inclusionAI/Universal-Manipulation-Exoskeleton/ume/robot/ume/v6_imu/models/assets/4040_ybimu.stl

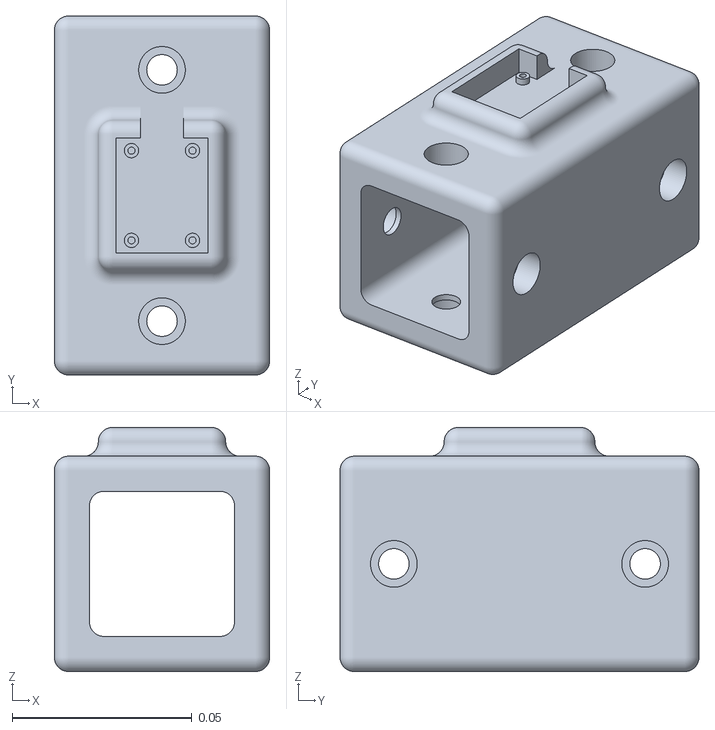
[picture p19: CAD file, 2026-07-16]
ume/robot/ume/v6_imu/models/assets/4040_ybimu.stl
0.06 x 0.1 x 0.068
