inclusionAI/Universal-Manipulation-Exoskeleton/ume/robot/openarm1/models/meshes/collision/arm/link0.stl

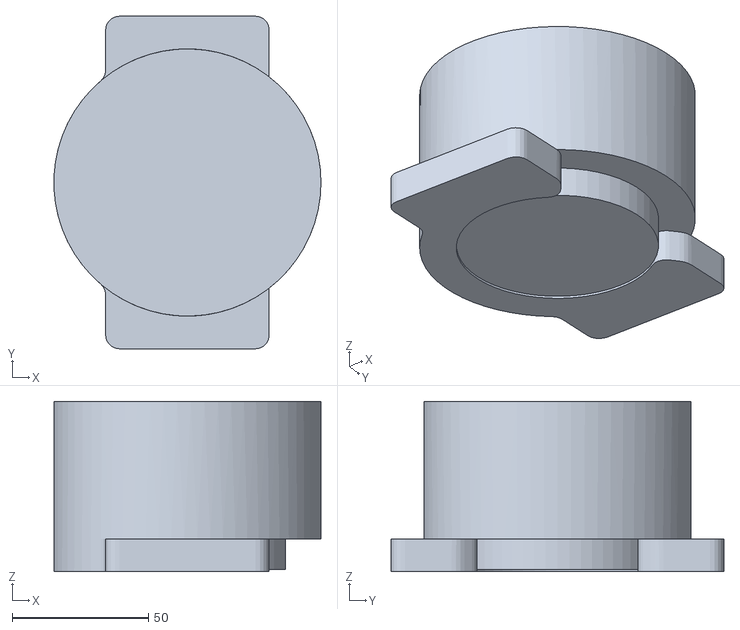
[picture p20: CAD file, 2026-07-16]
ume/robot/openarm1/models/meshes/collision/arm/link0.stl
97.9 x 122.0 x 62.5
