inclusionAI/Universal-Manipulation-Exoskeleton/ume/robot/openarm1/models/meshes/visual/arm/link5_0.obj

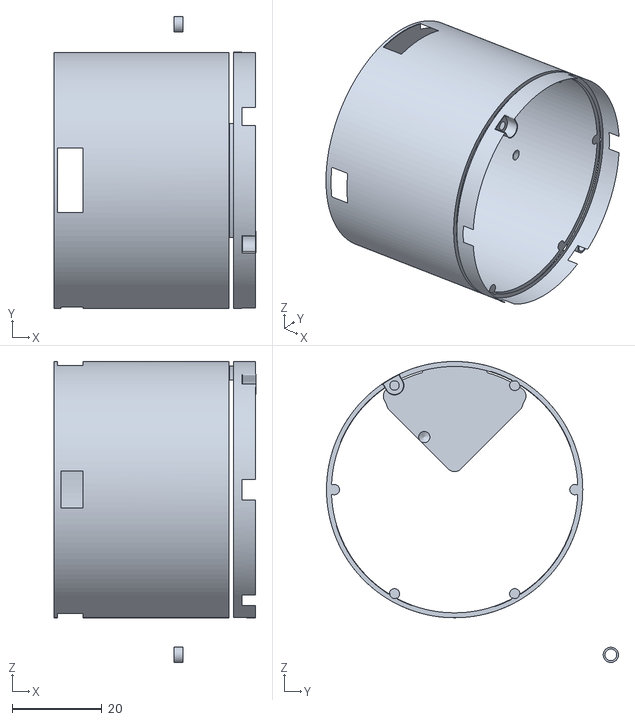
[picture p21: CAD file, 2026-07-16]
ume/robot/openarm1/models/meshes/visual/arm/link5_0.obj
44.9 x 64.9 x 66.9
