inclusionAI/Universal-Manipulation-Exoskeleton/ume/robot/openarm1/models/meshes/visual/body/body_link0_1.obj

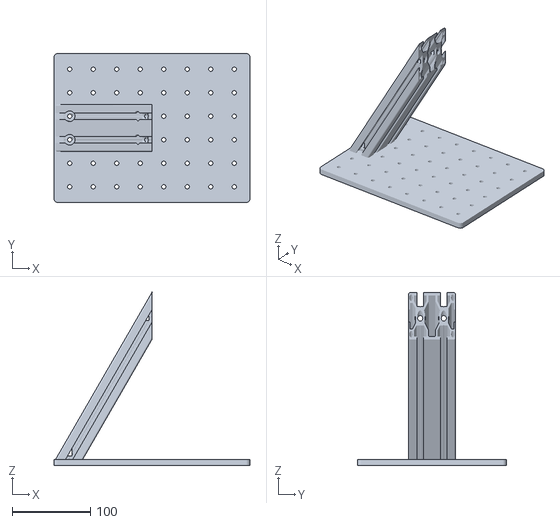
[picture p22: CAD file, 2026-07-16]
ume/robot/openarm1/models/meshes/visual/body/body_link0_1.obj
250.0 x 190.0 x 221.0
