inclusionAI/Universal-Manipulation-Exoskeleton/ume/robot/openarm1/models/meshes/visual/gripper/hand_1.obj

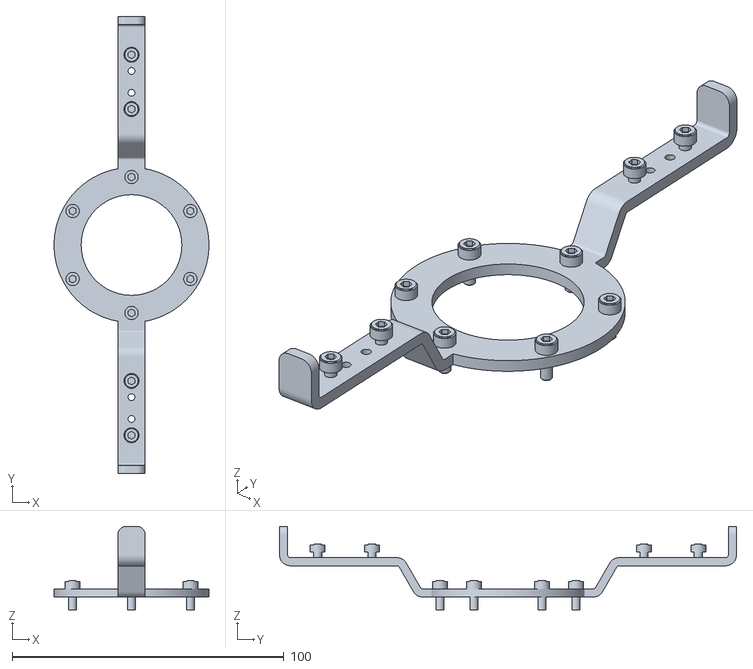
[picture p23: CAD file, 2026-07-16]
ume/robot/openarm1/models/meshes/visual/gripper/hand_1.obj
57.0 x 168.1 x 31.0
