inclusionAI/Universal-Manipulation-Exoskeleton/ume/robot/ume/v6_bimanual/models/assets/v6_xt30_2_2_50cm.stl

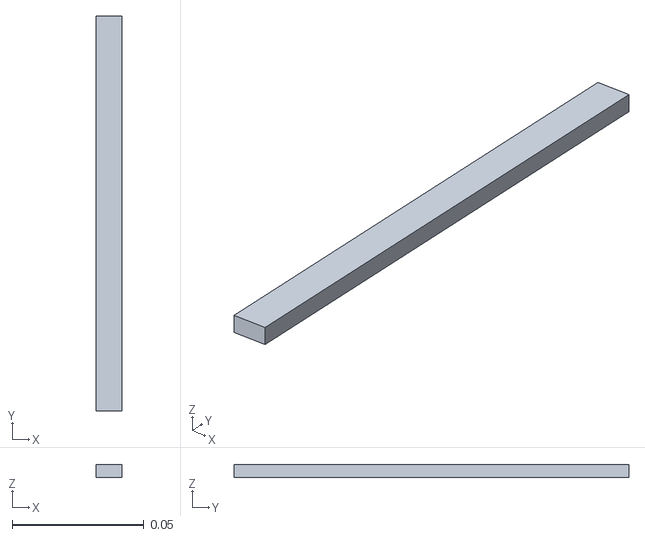
[picture p24: CAD file, 2026-07-16]
ume/robot/ume/v6_bimanual/models/assets/v6_xt30_2_2_50cm.stl
0.01 x 0.15 x 0.005
