inclusionAI/Universal-Manipulation-Exoskeleton/ume/robot/ume/v6_imu/models/assets/v6_4040_j1_loop_r.stl

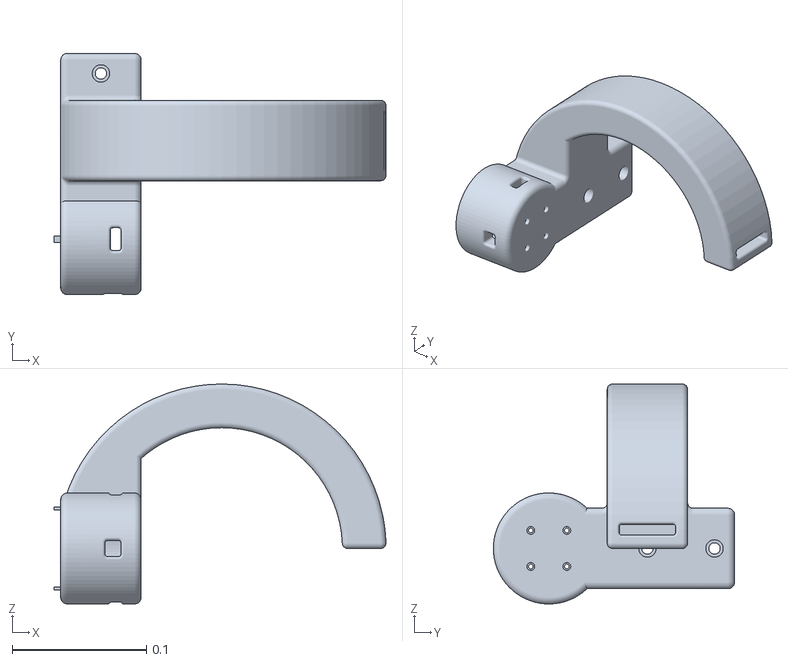
[picture p25: CAD file, 2026-07-16]
ume/robot/ume/v6_imu/models/assets/v6_4040_j1_loop_r.stl
0.248 x 0.18 x 0.164
