inclusionAI/Universal-Manipulation-Exoskeleton/ume/robot/openarm1/models/meshes/collision/arm/link1.stl

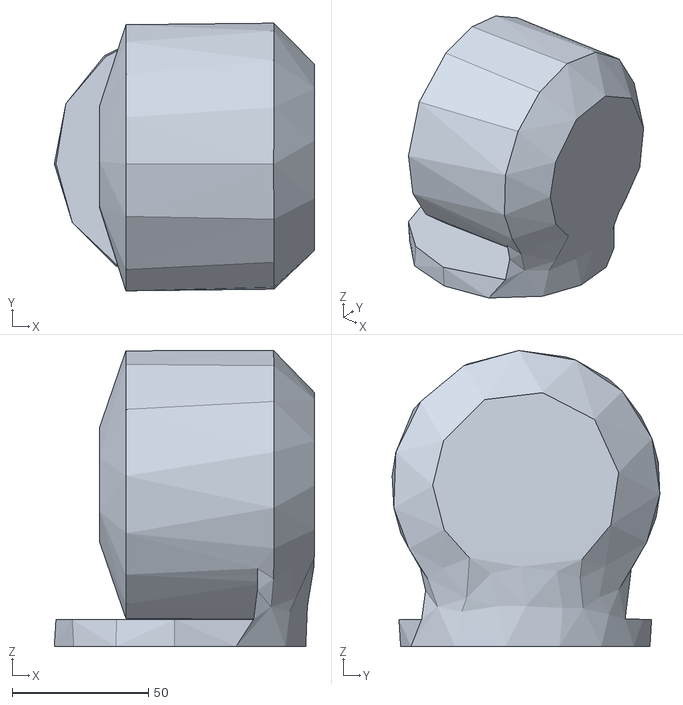
[picture p26: CAD file, 2026-07-16]
ume/robot/openarm1/models/meshes/collision/arm/link1.stl
95.7 x 98.4 x 108.8
