inclusionAI/Universal-Manipulation-Exoskeleton/ume/robot/openarm1/models/meshes/visual/arm/link2_2.obj

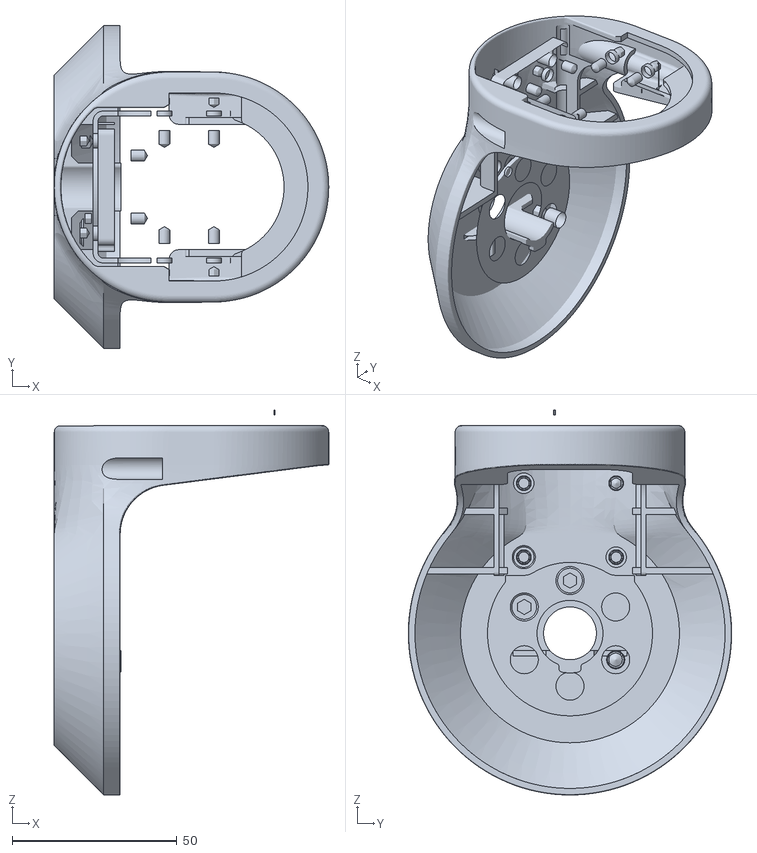
[picture p27: CAD file, 2026-07-16]
ume/robot/openarm1/models/meshes/visual/arm/link2_2.obj
83.2 x 98.0 x 116.7
