inclusionAI/Universal-Manipulation-Exoskeleton/ume/robot/openarm1/models/meshes/visual/body/body_link0_5.obj

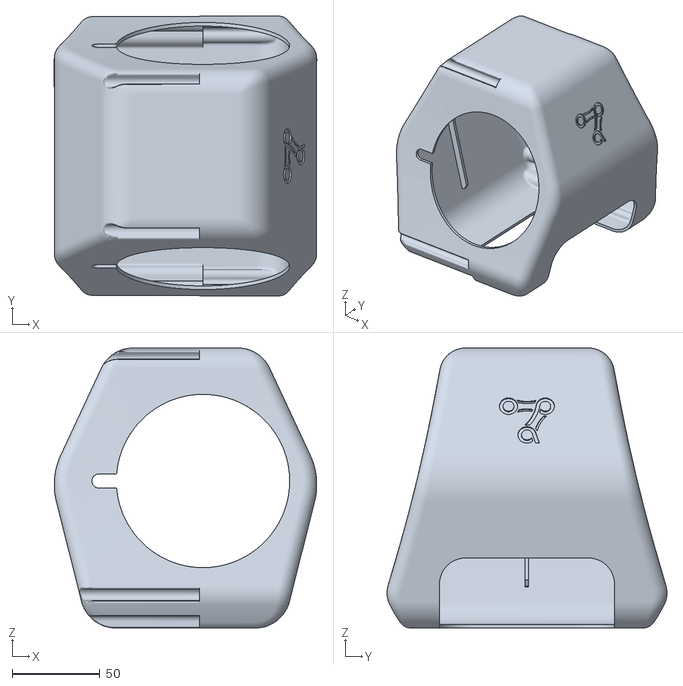
[picture p28: CAD file, 2026-07-16]
ume/robot/openarm1/models/meshes/visual/body/body_link0_5.obj
150.0 x 160.0 x 160.0
