inclusionAI/Universal-Manipulation-Exoskeleton/ume/robot/openarm1/models/meshes/visual/gripper/finger_1.obj

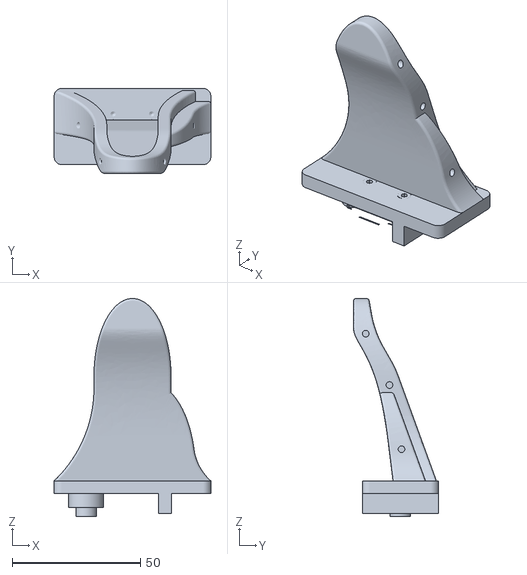
[picture p29: CAD file, 2026-07-16]
ume/robot/openarm1/models/meshes/visual/gripper/finger_1.obj
61.0 x 33.2 x 84.9
