inclusionAI/Universal-Manipulation-Exoskeleton/ume/robot/ume/ume_step/ume_v6_bimanual - v6_2020_J4_L.step

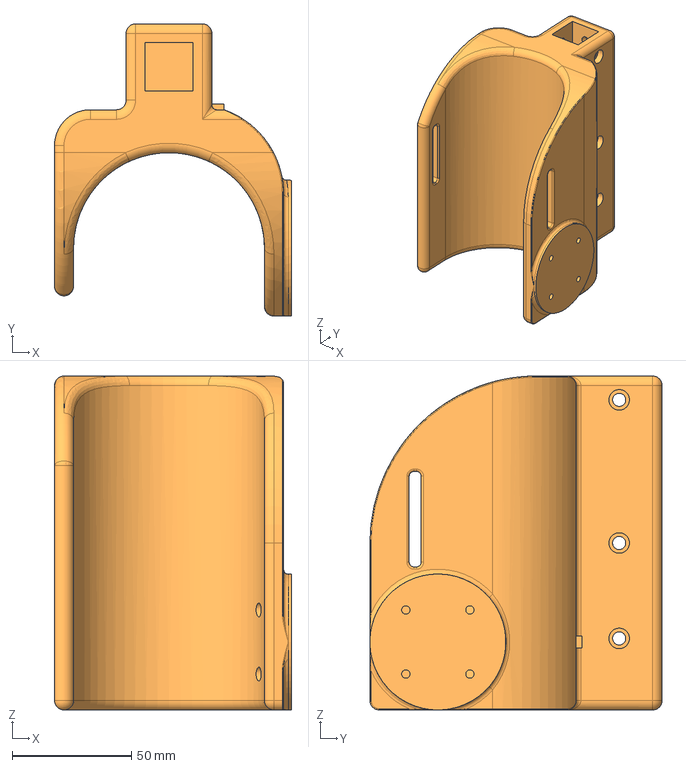
[picture p30: CAD file, 2026-07-16]
ume/robot/ume/ume_step/ume_v6_bimanual - v6_2020_J4_L.step
99.3 x 122.5 x 140.0 mm
