inclusionAI/Universal-Manipulation-Exoskeleton/ume/robot/ume/v6_bimanual/models/assets/dm_j4340_2ec.stl

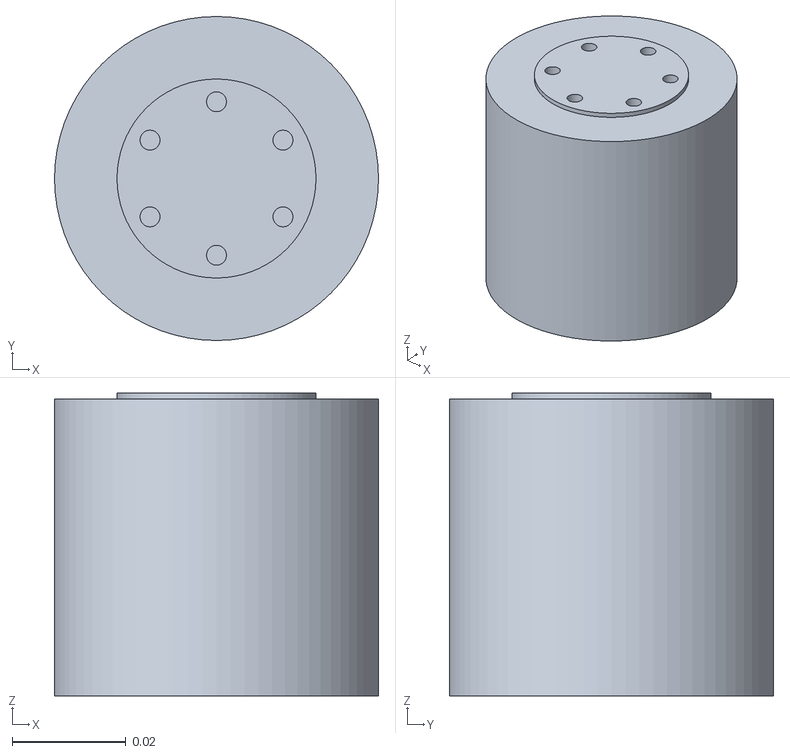
[picture p31: CAD file, 2026-07-16]
ume/robot/ume/v6_bimanual/models/assets/dm_j4340_2ec.stl
0.057 x 0.057 x 0.0533
