inclusionAI/Universal-Manipulation-Exoskeleton/ume/robot/ume/v6_imu/models/assets/v5_wrist_j6_j7.stl

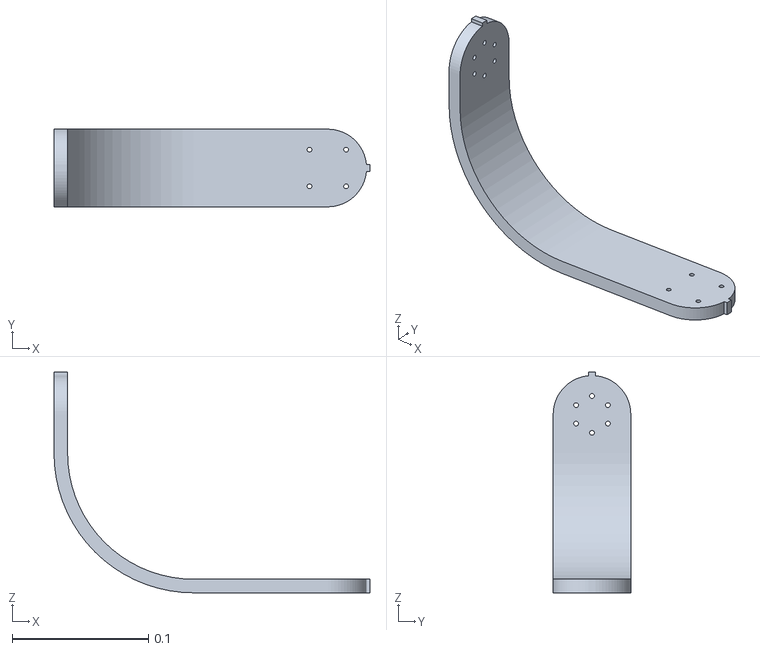
[picture p32: CAD file, 2026-07-16]
ume/robot/ume/v6_imu/models/assets/v5_wrist_j6_j7.stl
0.232 x 0.057 x 0.162
