inclusionAI/Universal-Manipulation-Exoskeleton/ume/robot/openarm1/models/meshes/collision/arm/link7.stl

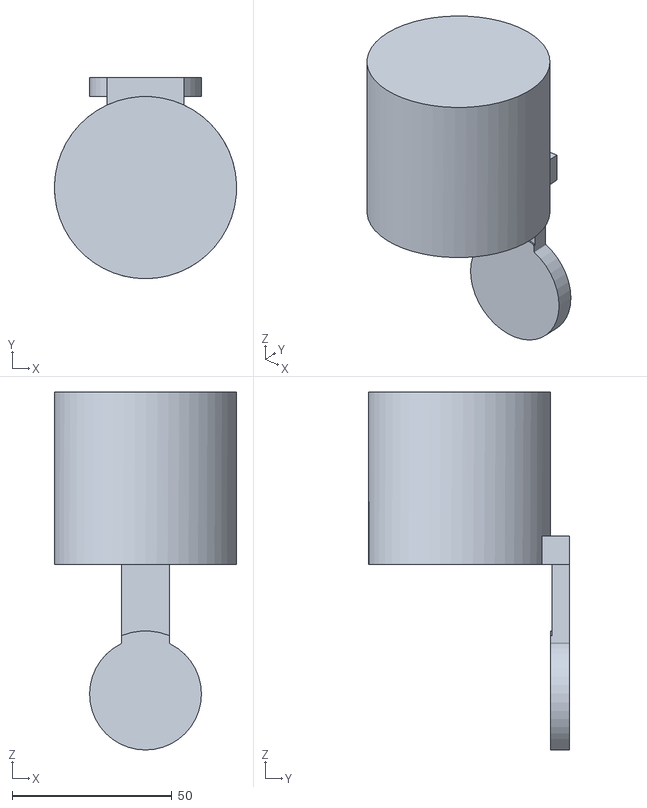
[picture p33: CAD file, 2026-07-16]
ume/robot/openarm1/models/meshes/collision/arm/link7.stl
57.0 x 63.0 x 112.0
