inclusionAI/Universal-Manipulation-Exoskeleton/ume/robot/openarm1/models/meshes/visual/arm/link7_1.obj

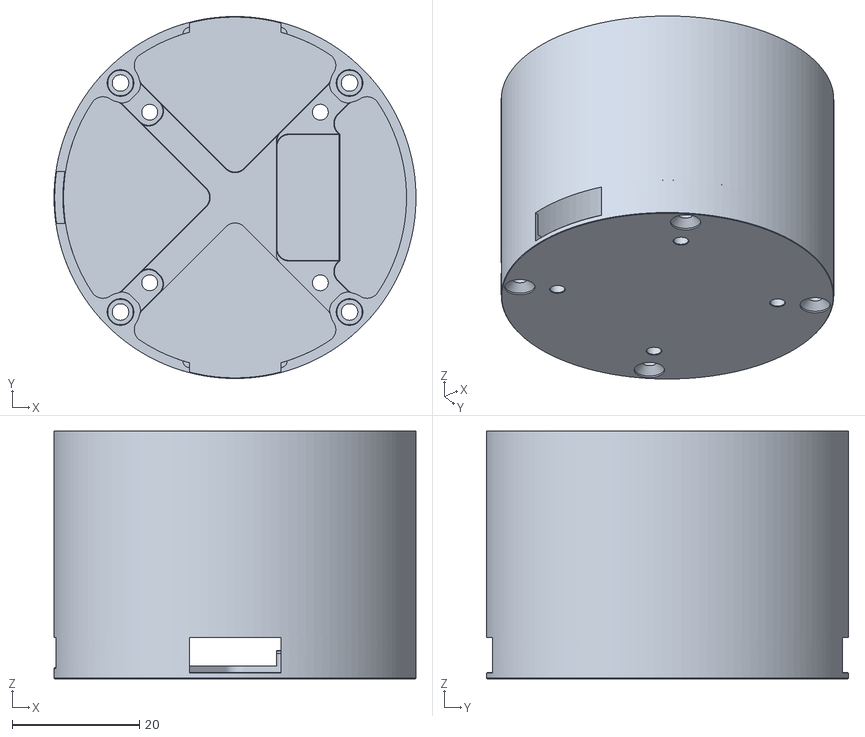
[picture p34: CAD file, 2026-07-16]
ume/robot/openarm1/models/meshes/visual/arm/link7_1.obj
57.0 x 57.0 x 39.0
