inclusionAI/Universal-Manipulation-Exoskeleton/ume/robot/openarm1/models/meshes/visual/body/body_link0_3.obj

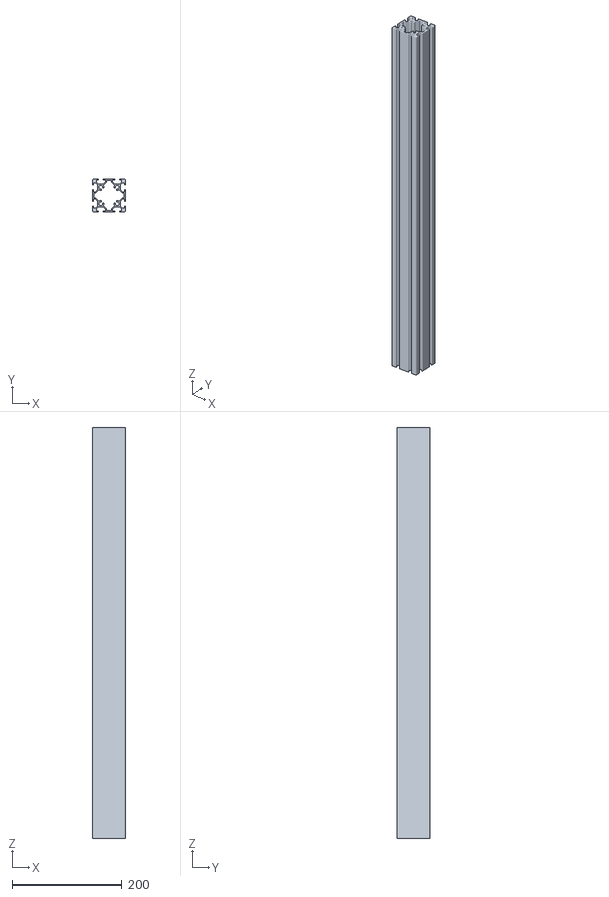
[picture p35: CAD file, 2026-07-16]
ume/robot/openarm1/models/meshes/visual/body/body_link0_3.obj
60.0 x 60.0 x 750.0
