inclusionAI/Universal-Manipulation-Exoskeleton/ume/robot/ume/v6_bimanual/models/assets/v6_wrist_j5_j6.stl

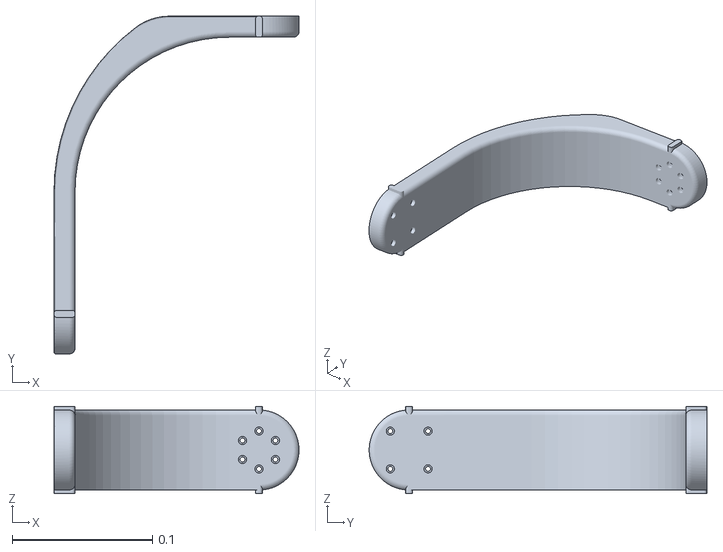
[picture p36: CAD file, 2026-07-16]
ume/robot/ume/v6_bimanual/models/assets/v6_wrist_j5_j6.stl
0.174 x 0.24 x 0.062
