inclusionAI/Universal-Manipulation-Exoskeleton/ume/robot/ume/v6_imu/models/assets/v6_20_j2.stl

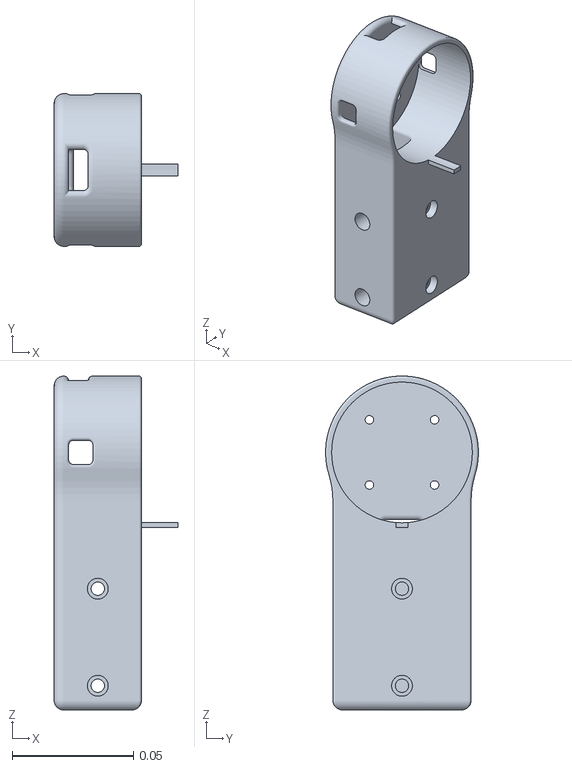
[picture p37: CAD file, 2026-07-16]
ume/robot/ume/v6_imu/models/assets/v6_20_j2.stl
0.051 x 0.063 x 0.138
