inclusionAI/Universal-Manipulation-Exoskeleton/ume/robot/openarm1/models/meshes/collision/arm/link4.stl

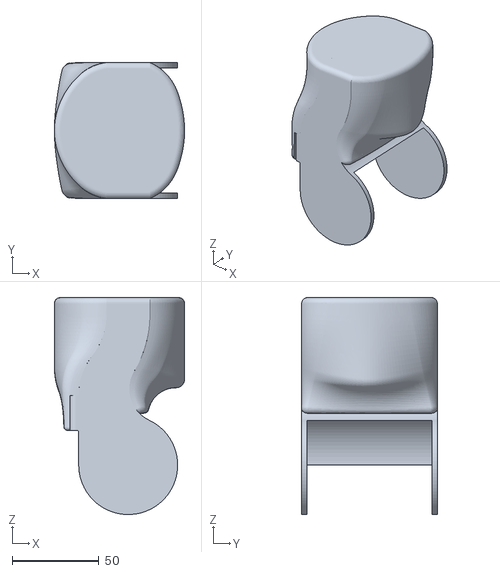
[picture p38: CAD file, 2026-07-16]
ume/robot/openarm1/models/meshes/collision/arm/link4.stl
75.0 x 78.2 x 125.0
