inclusionAI/Universal-Manipulation-Exoskeleton/ume/robot/openarm1/models/meshes/visual/arm/link4_2.obj

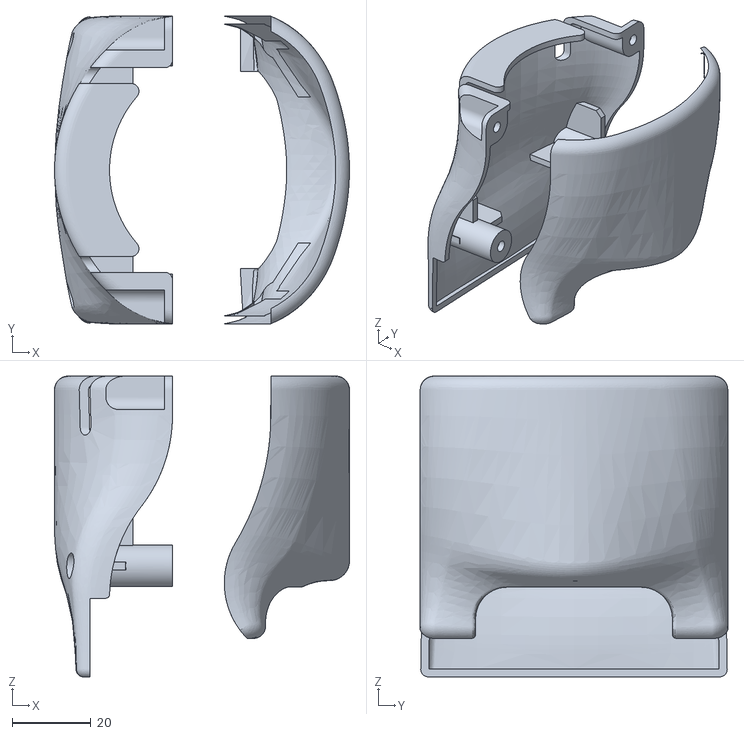
[picture p39: CAD file, 2026-07-16]
ume/robot/openarm1/models/meshes/visual/arm/link4_2.obj
75.0 x 78.2 x 76.5
