inclusionAI/Universal-Manipulation-Exoskeleton/ume/robot/openarm1/models/meshes/visual/body/body_link0_4.obj

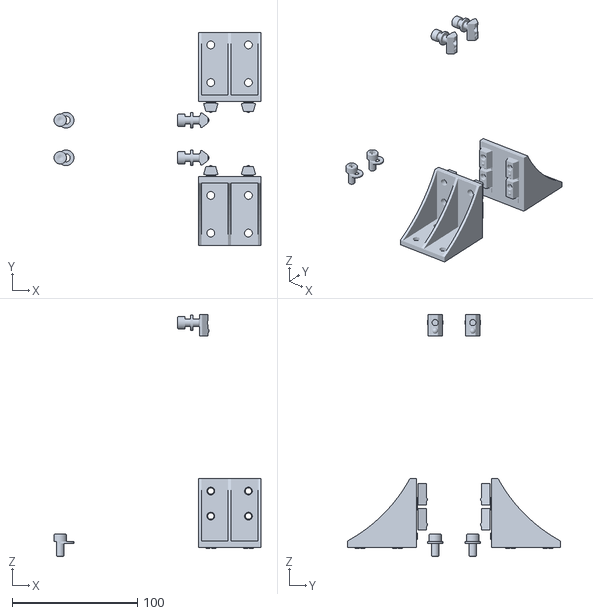
[picture p40: CAD file, 2026-07-16]
ume/robot/openarm1/models/meshes/visual/body/body_link0_4.obj
165.0 x 170.0 x 192.9
