inclusionAI/Universal-Manipulation-Exoskeleton/ume/robot/openarm1/models/meshes/collision/arm/link3.stl

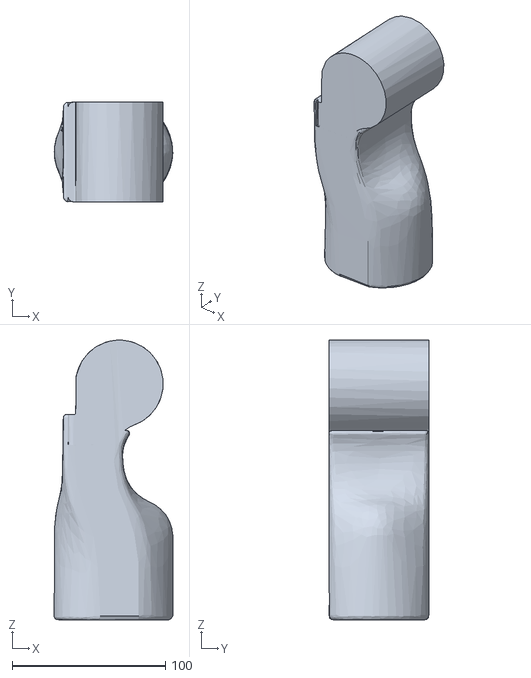
[picture p41: CAD file, 2026-07-16]
ume/robot/openarm1/models/meshes/collision/arm/link3.stl
77.3 x 65.0 x 182.6
