inclusionAI/Universal-Manipulation-Exoskeleton/ume/robot/openarm1/models/meshes/visual/arm/link1_3.obj

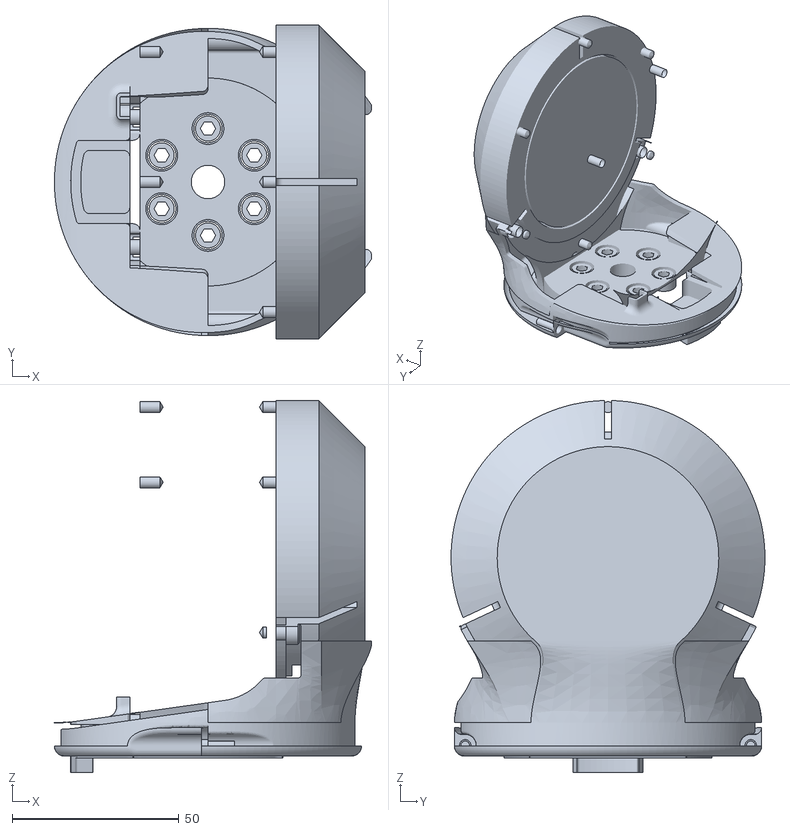
[picture p42: CAD file, 2026-07-16]
ume/robot/openarm1/models/meshes/visual/arm/link1_3.obj
95.0 x 94.0 x 111.4
