inclusionAI/Universal-Manipulation-Exoskeleton/ume/robot/ume/v6_bimanual/models/assets/v5_4040_j1.stl

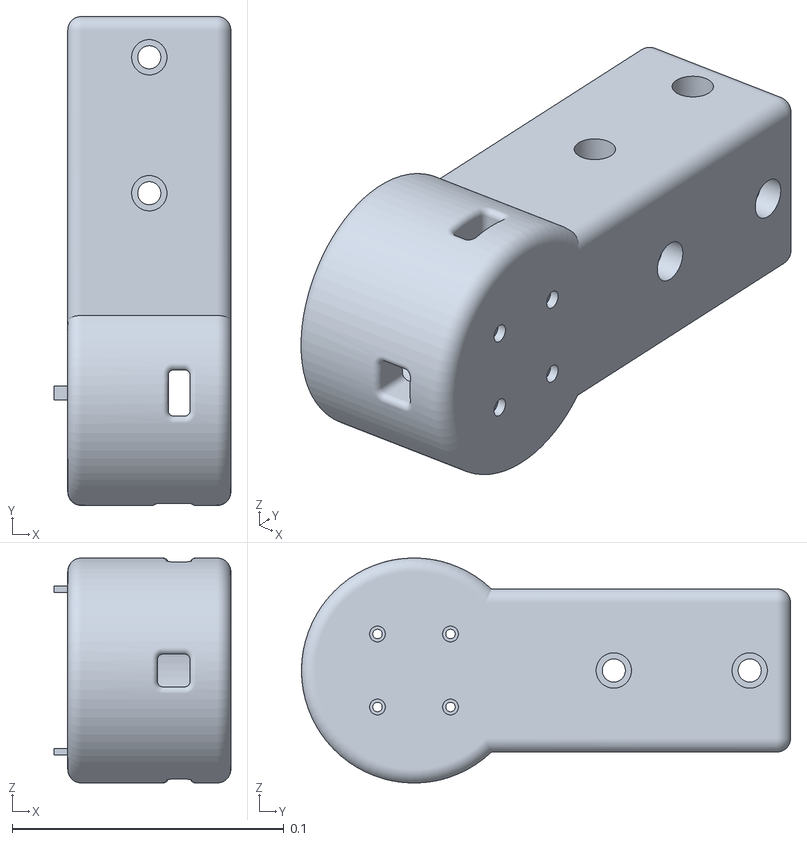
[picture p43: CAD file, 2026-07-16]
ume/robot/ume/v6_bimanual/models/assets/v5_4040_j1.stl
0.065 x 0.18 x 0.0828
