inclusionAI/Universal-Manipulation-Exoskeleton/ume/robot/openarm1/models/meshes/collision/arm/link5.stl

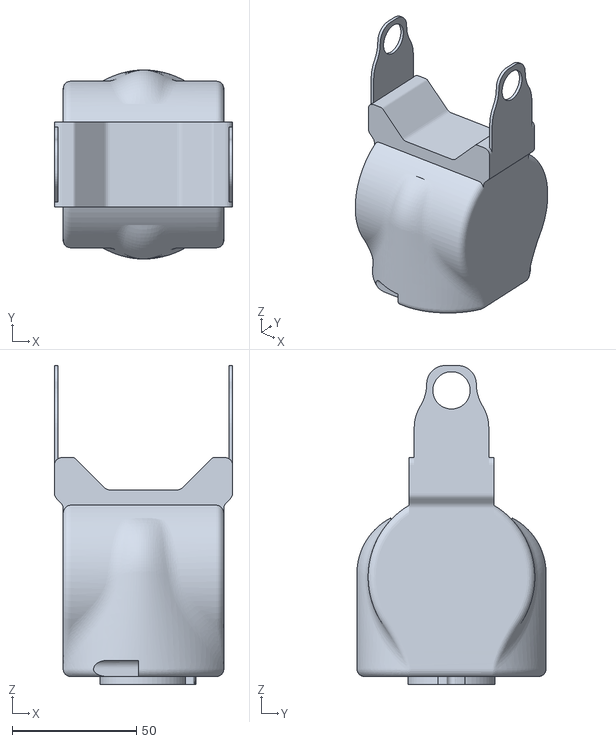
[picture p44: CAD file, 2026-07-16]
ume/robot/openarm1/models/meshes/collision/arm/link5.stl
71.6 x 76.0 x 128.2
