inclusionAI/Universal-Manipulation-Exoskeleton/ume/robot/openarm1/models/meshes/visual/arm/link1_1.obj

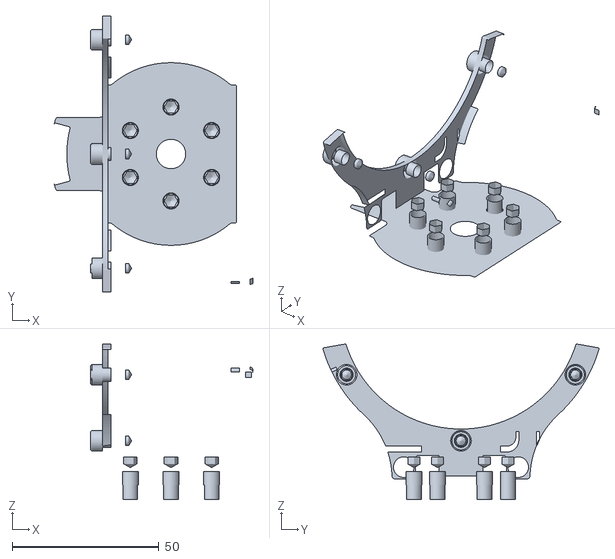
[picture p45: CAD file, 2026-07-16]
ume/robot/openarm1/models/meshes/visual/arm/link1_1.obj
67.7 x 94.0 x 53.4
