inclusionAI/Universal-Manipulation-Exoskeleton/ume/robot/openarm1/models/meshes/visual/arm/link3_2.obj

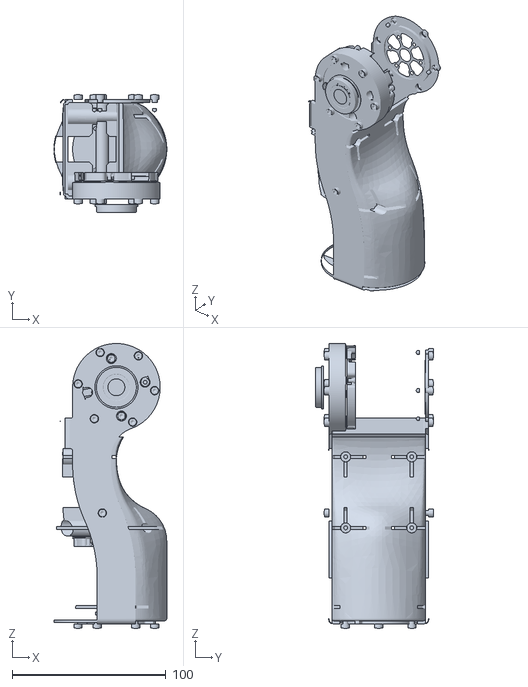
[picture p46: CAD file, 2026-07-16]
ume/robot/openarm1/models/meshes/visual/arm/link3_2.obj
73.3 x 76.5 x 185.5
