inclusionAI/Universal-Manipulation-Exoskeleton/ume/robot/ume/v6_bimanual/models/assets/v6_2020_j4_r.stl

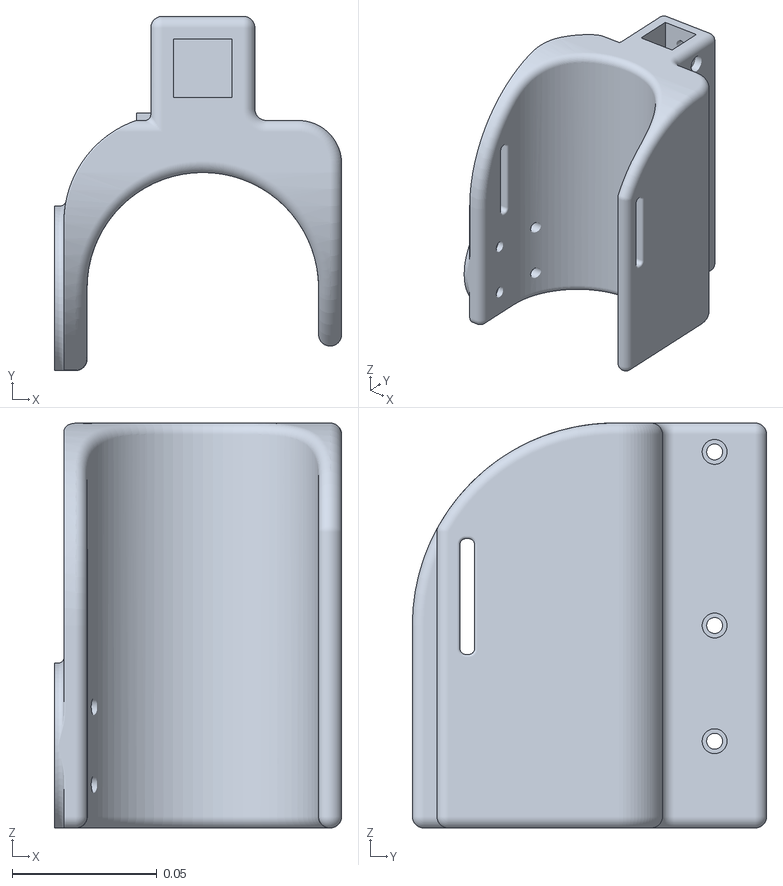
[picture p47: CAD file, 2026-07-16]
ume/robot/ume/v6_bimanual/models/assets/v6_2020_j4_r.stl
0.0994 x 0.123 x 0.14
