inclusionAI/Universal-Manipulation-Exoskeleton/ume/robot/ume/v6_imu/models/assets/4040_t_bracket.stl

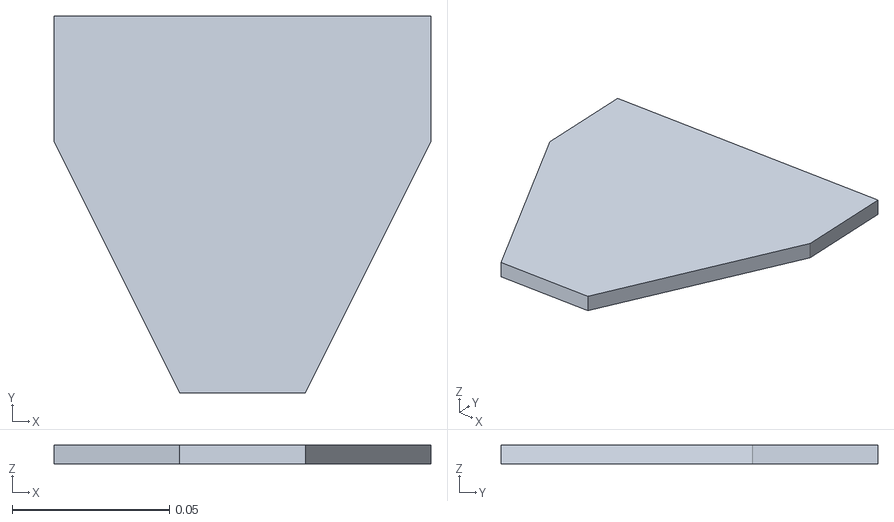
[picture p48: CAD file, 2026-07-16]
ume/robot/ume/v6_imu/models/assets/4040_t_bracket.stl
0.12 x 0.12 x 0.006
