inclusionAI/Universal-Manipulation-Exoskeleton/ume/robot/openarm1/models/meshes/visual/arm/link1_0.obj

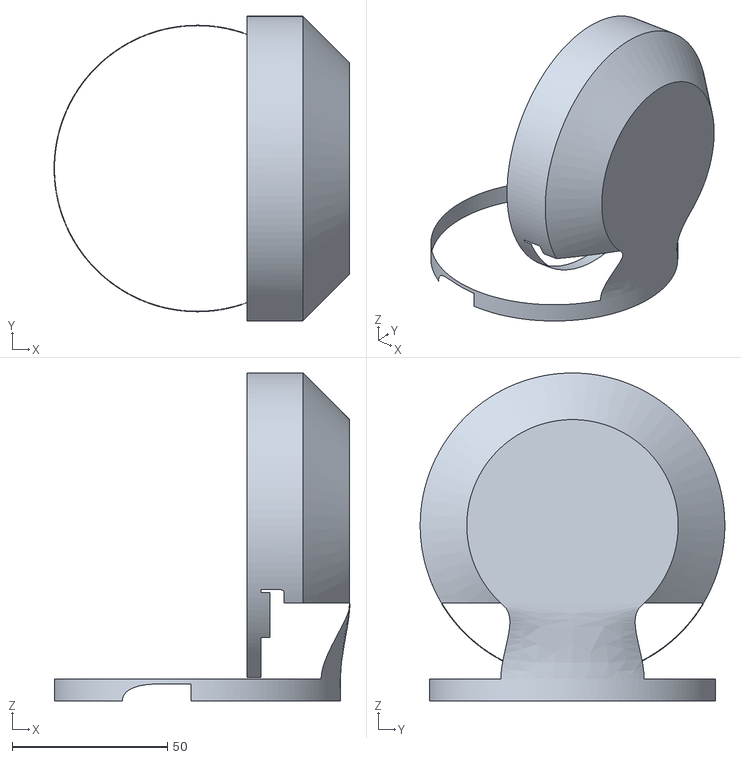
[picture p49: CAD file, 2026-07-16]
ume/robot/openarm1/models/meshes/visual/arm/link1_0.obj
95.0 x 98.0 x 105.5
