inclusionAI/Universal-Manipulation-Exoskeleton/ume/robot/ume/v6_bimanual/models/assets/v6_20_j3.stl

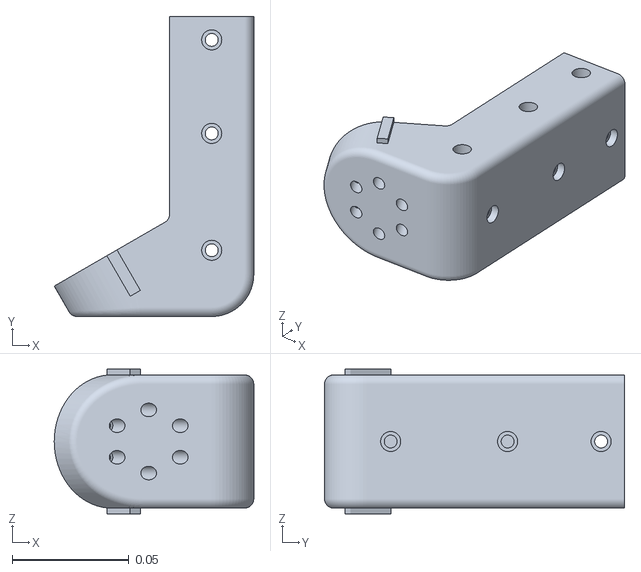
[picture p50: CAD file, 2026-07-16]
ume/robot/ume/v6_bimanual/models/assets/v6_20_j3.stl
0.0854 x 0.128 x 0.062
