inclusionAI/Universal-Manipulation-Exoskeleton/ume/robot/ume/v6_imu/models/assets/dm_j4310_2ec.stl

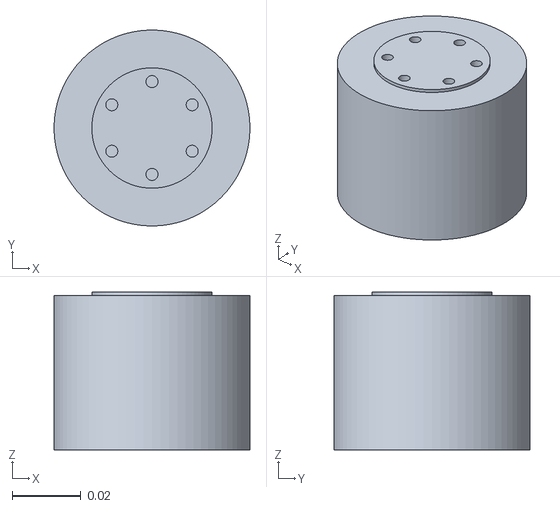
[picture p51: CAD file, 2026-07-16]
ume/robot/ume/v6_imu/models/assets/dm_j4310_2ec.stl
0.057 x 0.057 x 0.0459
