inclusionAI/Universal-Manipulation-Exoskeleton/ume/robot/openarm1/models/meshes/visual/arm/link5_2.obj

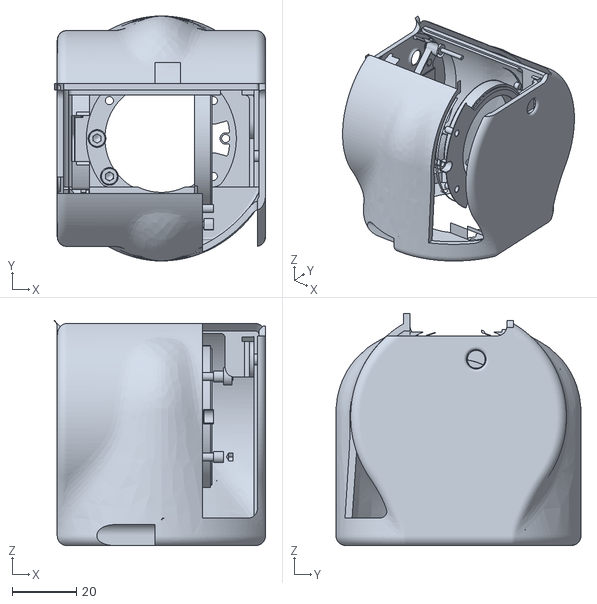
[picture p52: CAD file, 2026-07-16]
ume/robot/openarm1/models/meshes/visual/arm/link5_2.obj
65.5 x 76.0 x 72.0
