inclusionAI/Universal-Manipulation-Exoskeleton/ume/robot/openarm1/models/meshes/visual/arm/link3_0.obj

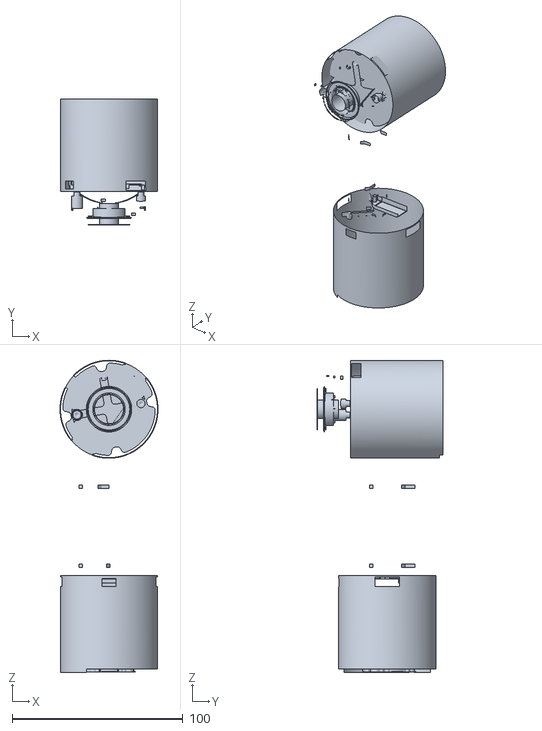
[picture p53: CAD file, 2026-07-16]
ume/robot/openarm1/models/meshes/visual/arm/link3_0.obj
57.0 x 73.5 x 182.5
