inclusionAI/Universal-Manipulation-Exoskeleton/ume/robot/ume/v6_bimanual/models/assets/v6_j1_20.stl

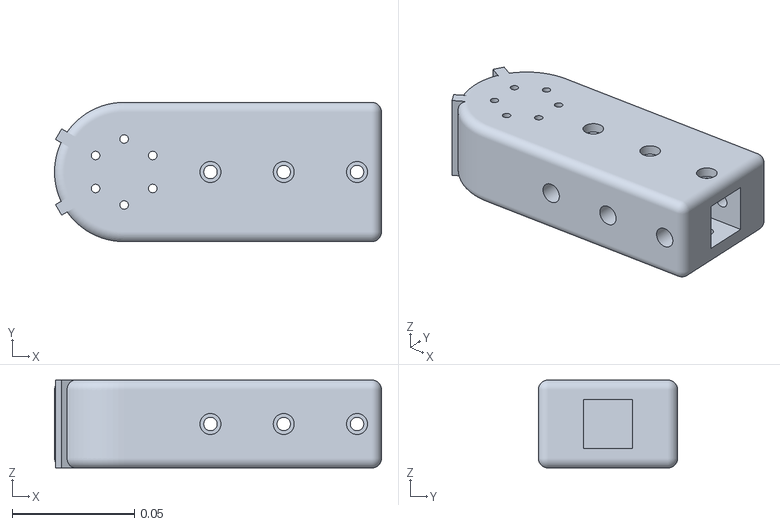
[picture p54: CAD file, 2026-07-16]
ume/robot/ume/v6_bimanual/models/assets/v6_j1_20.stl
0.134 x 0.057 x 0.036
