inclusionAI/Universal-Manipulation-Exoskeleton/ume/robot/openarm1/models/meshes/visual/arm/link2_0.obj

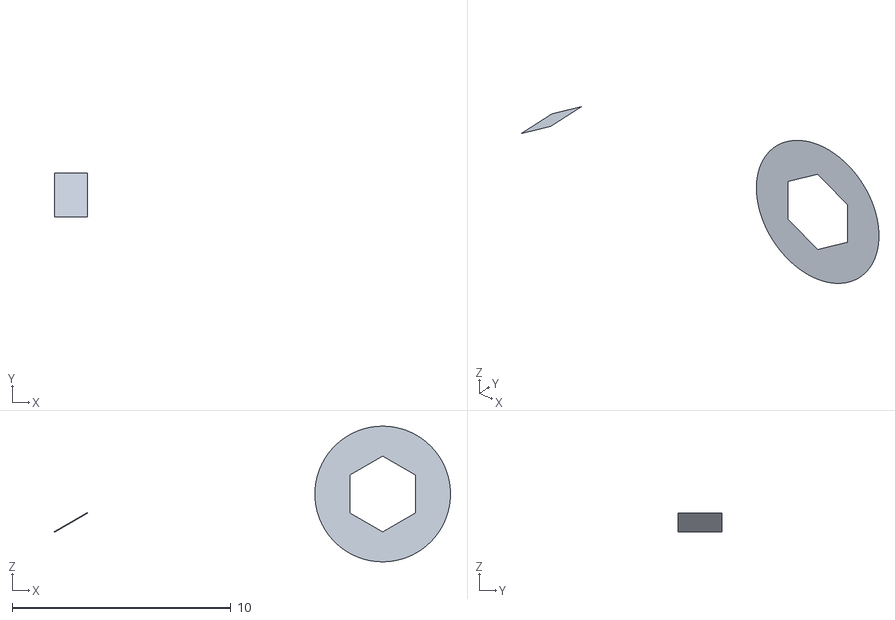
[picture p55: CAD file, 2026-07-16]
ume/robot/openarm1/models/meshes/visual/arm/link2_0.obj
18.1 x 2.00 x 6.20
