inclusionAI/Universal-Manipulation-Exoskeleton/ume/robot/ume/ume_step/ume_v6_bimanual - 2020x10cm.step

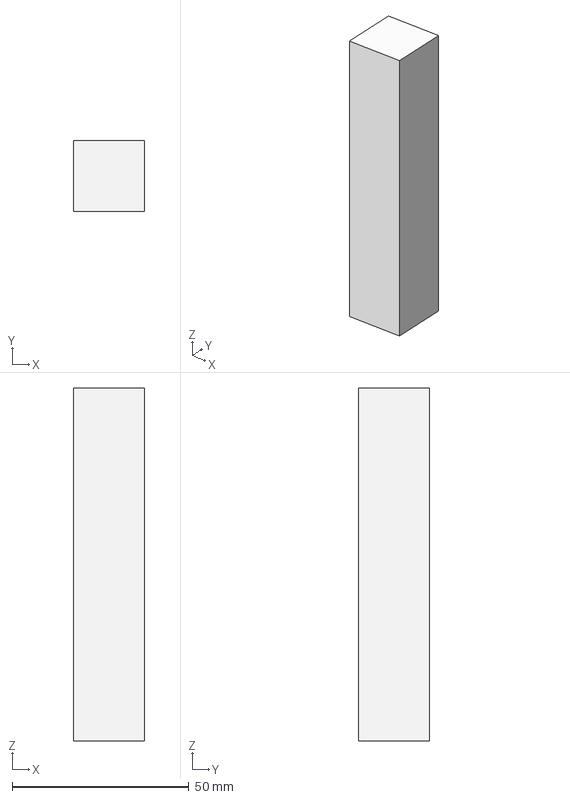
[picture p56: CAD file, 2026-07-16]
ume/robot/ume/ume_step/ume_v6_bimanual - 2020x10cm.step
20.0 x 20.0 x 100.0 mm
