inclusionAI/Universal-Manipulation-Exoskeleton/ume/robot/ume/v6_bimanual/models/assets/v6_j3_2020_l.stl

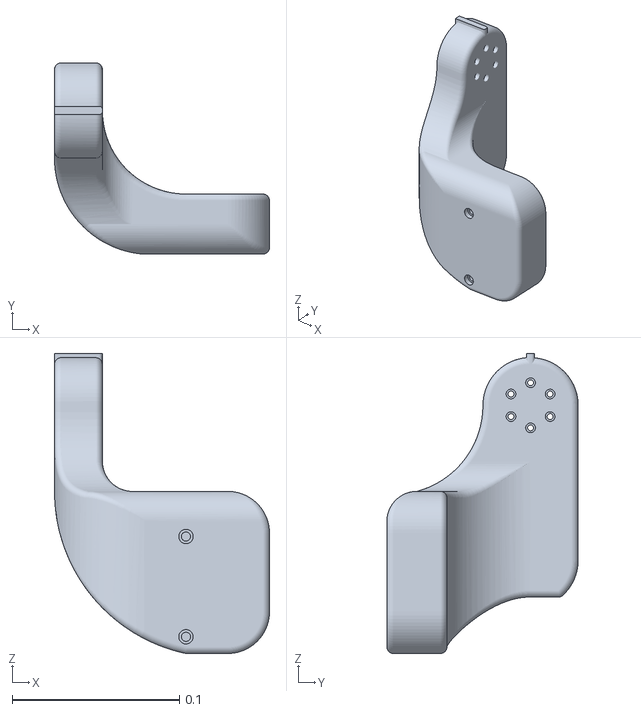
[picture p57: CAD file, 2026-07-16]
ume/robot/ume/v6_bimanual/models/assets/v6_j3_2020_l.stl
0.129 x 0.115 x 0.179
