inclusionAI/Universal-Manipulation-Exoskeleton/ume/robot/openarm1/models/meshes/visual/arm/link7_0.obj

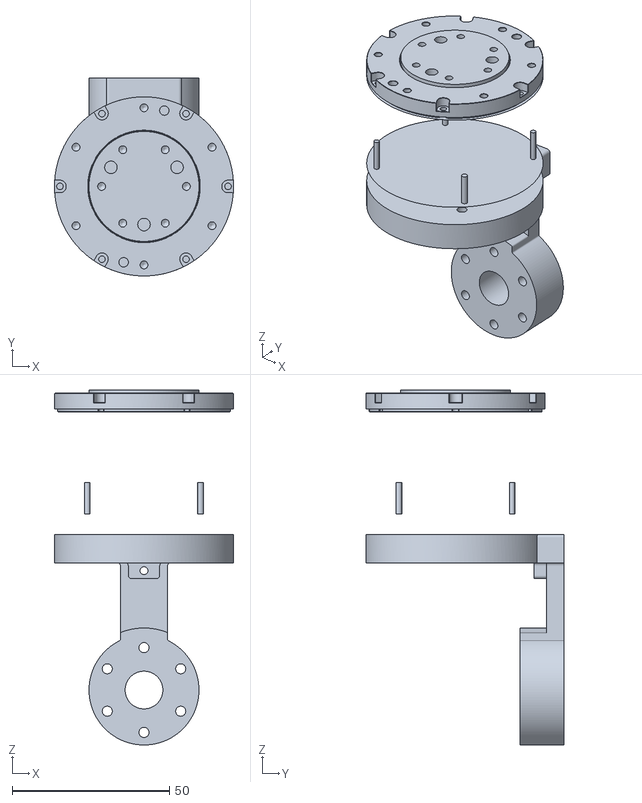
[picture p58: CAD file, 2026-07-16]
ume/robot/openarm1/models/meshes/visual/arm/link7_0.obj
57.0 x 63.0 x 113.0
