inclusionAI/Universal-Manipulation-Exoskeleton/ume/robot/openarm1/models/meshes/visual/arm/link4_0.obj

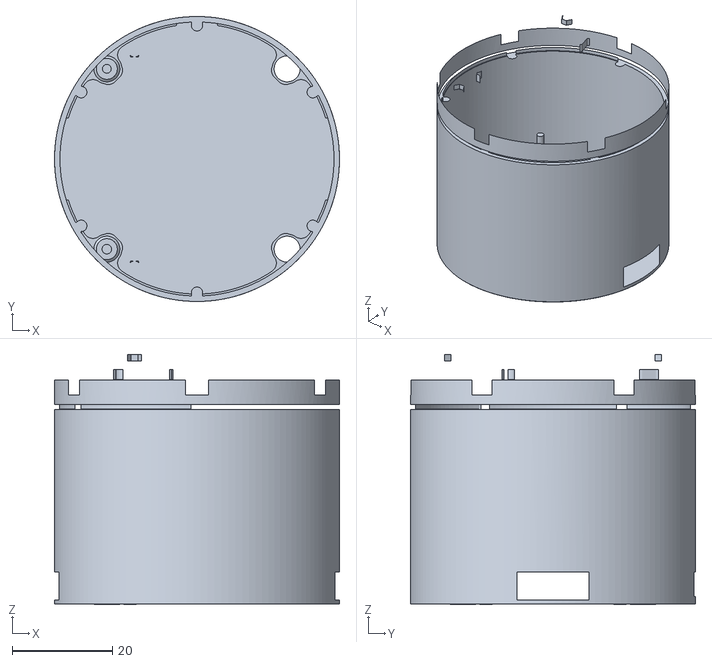
[picture p59: CAD file, 2026-07-16]
ume/robot/openarm1/models/meshes/visual/arm/link4_0.obj
57.0 x 57.0 x 50.0
