inclusionAI/Universal-Manipulation-Exoskeleton/ume/robot/openarm1/models/meshes/visual/arm/link5_1.obj

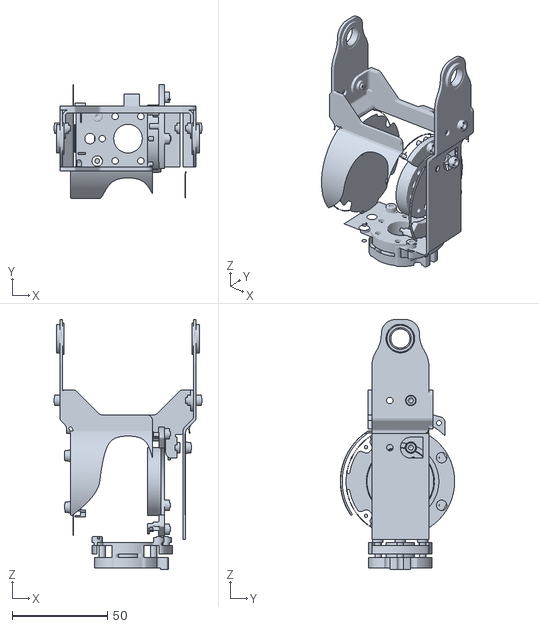
[picture p60: CAD file, 2026-07-16]
ume/robot/openarm1/models/meshes/visual/arm/link5_1.obj
77.6 x 60.0 x 131.2
