inclusionAI/Universal-Manipulation-Exoskeleton/ume/robot/ume/ume_step/ume_v6_bimanual - v5_J8_4finger.step

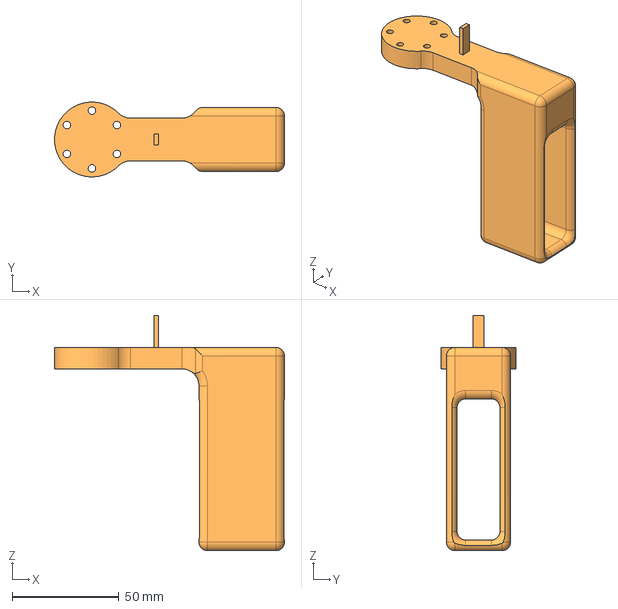
[picture p61: CAD file, 2026-07-16]
ume/robot/ume/ume_step/ume_v6_bimanual - v5_J8_4finger.step
107.5 x 35.0 x 110.0 mm
