inclusionAI/Universal-Manipulation-Exoskeleton/ume/robot/openarm1/models/meshes/visual/arm/link4_1.obj

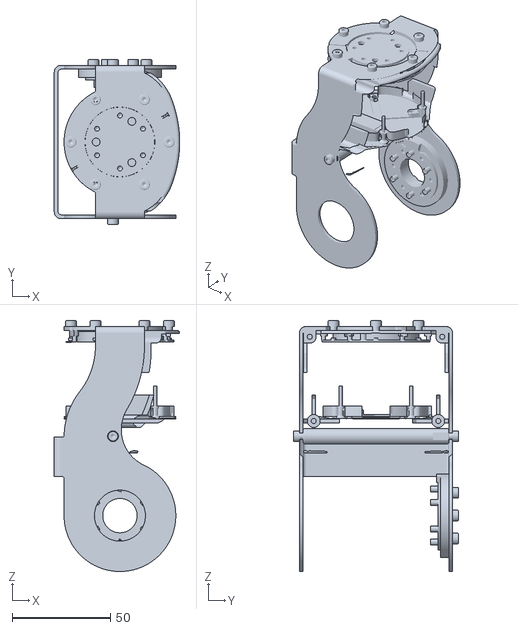
[picture p62: CAD file, 2026-07-16]
ume/robot/openarm1/models/meshes/visual/arm/link4_1.obj
64.0 x 84.2 x 128.0
