inclusionAI/Universal-Manipulation-Exoskeleton/ume/robot/ume/v6_bimanual/models/assets/v5_wrist_j7_leader_gripper_r.stl

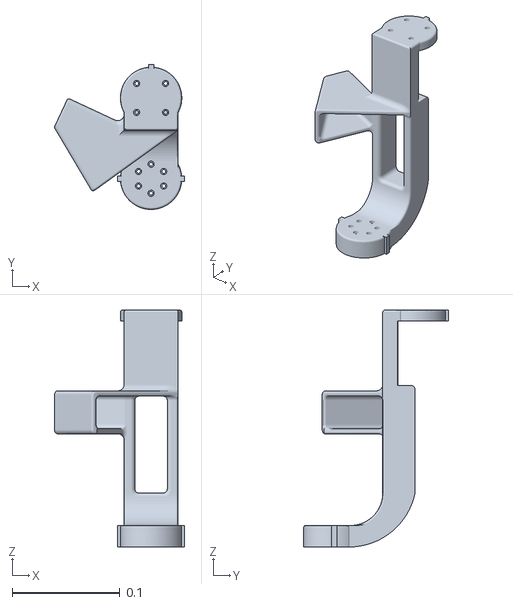
[picture p63: CAD file, 2026-07-16]
ume/robot/ume/v6_bimanual/models/assets/v5_wrist_j7_leader_gripper_r.stl
0.121 x 0.134 x 0.22
