inclusionAI/Universal-Manipulation-Exoskeleton/ume/robot/openarm1/models/meshes/visual/arm/link0_1.obj

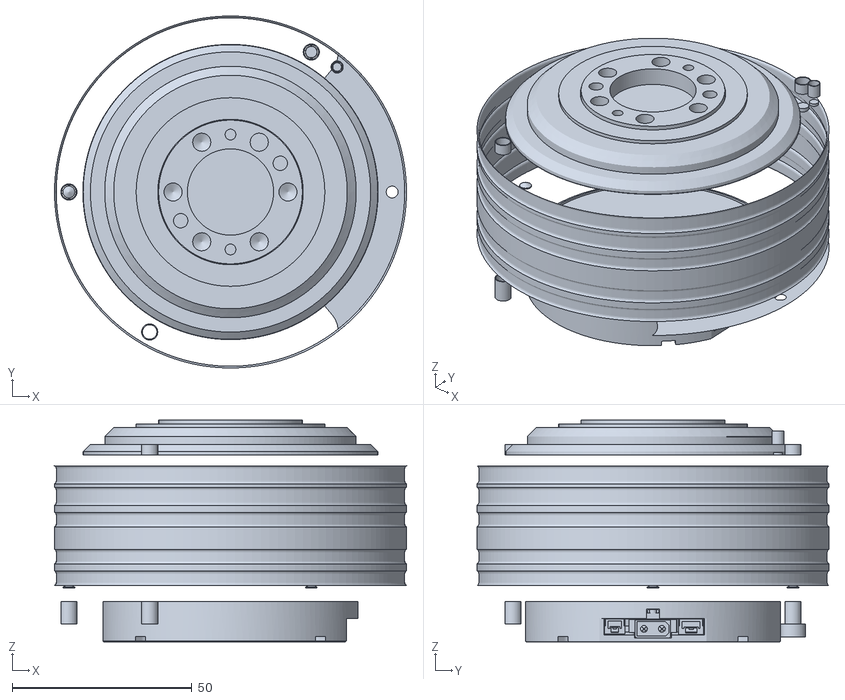
[picture p64: CAD file, 2026-07-16]
ume/robot/openarm1/models/meshes/visual/arm/link0_1.obj
98.0 x 98.0 x 61.7
