inclusionAI/Universal-Manipulation-Exoskeleton/ume/robot/ume/v6_bimanual/models/assets/v5_j8_4finger.stl

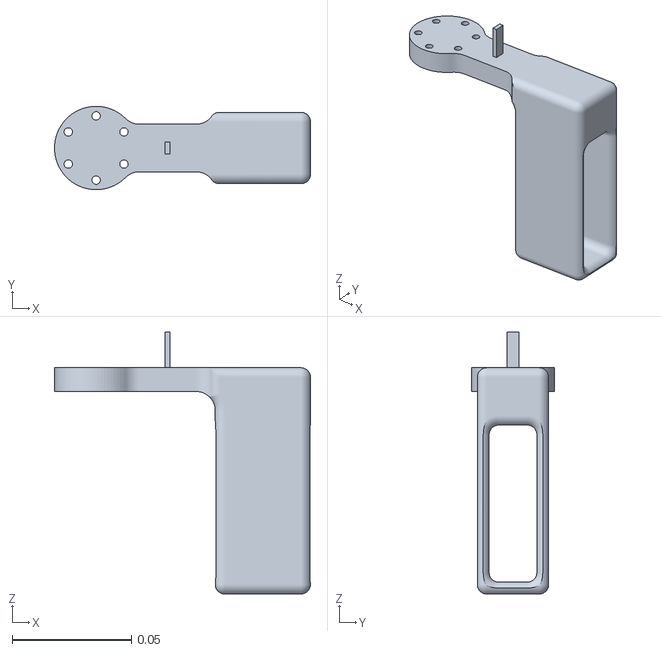
[picture p65: CAD file, 2026-07-16]
ume/robot/ume/v6_bimanual/models/assets/v5_j8_4finger.stl
0.107 x 0.035 x 0.11
