inclusionAI/Universal-Manipulation-Exoskeleton/ume/robot/openarm1/models/meshes/visual/arm/link6_0.obj

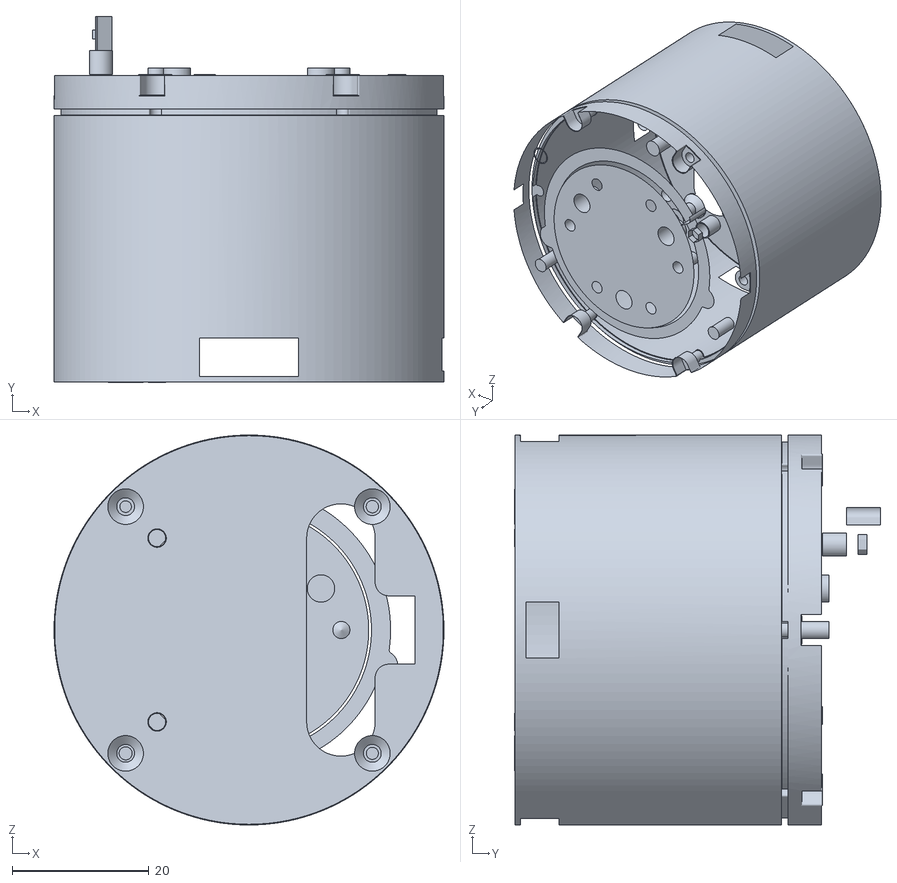
[picture p66: CAD file, 2026-07-16]
ume/robot/openarm1/models/meshes/visual/arm/link6_0.obj
57.0 x 53.5 x 57.0
