inclusionAI/Universal-Manipulation-Exoskeleton/ume/robot/openarm1/models/meshes/visual/arm/link1_2.obj

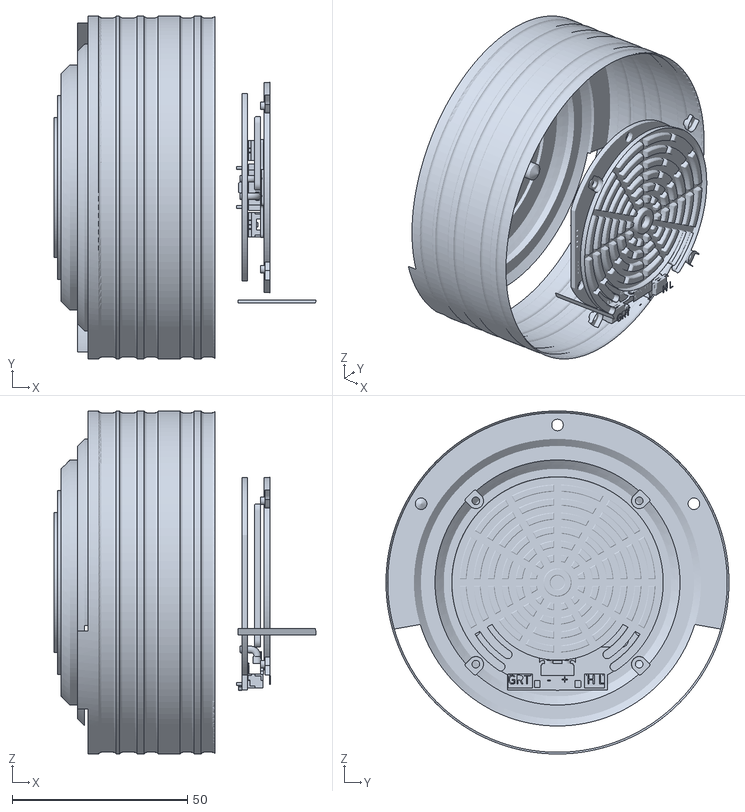
[picture p67: CAD file, 2026-07-16]
ume/robot/openarm1/models/meshes/visual/arm/link1_2.obj
74.8 x 98.0 x 98.0
