inclusionAI/Universal-Manipulation-Exoskeleton/ume/robot/ume/ume_step/ume_v6_bimanual - v6_J1_20.step

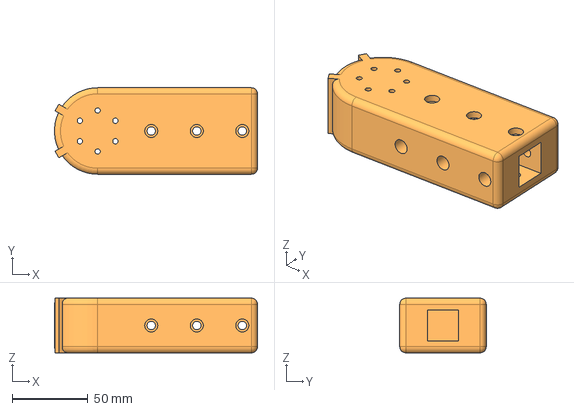
[picture p68: CAD file, 2026-07-16]
ume/robot/ume/ume_step/ume_v6_bimanual - v6_J1_20.step
133.7 x 57.0 x 36.0 mm
