inclusionAI/Universal-Manipulation-Exoskeleton/ume/robot/ume/ume_step/ume_v6_bimanual - v6_20_J2.step

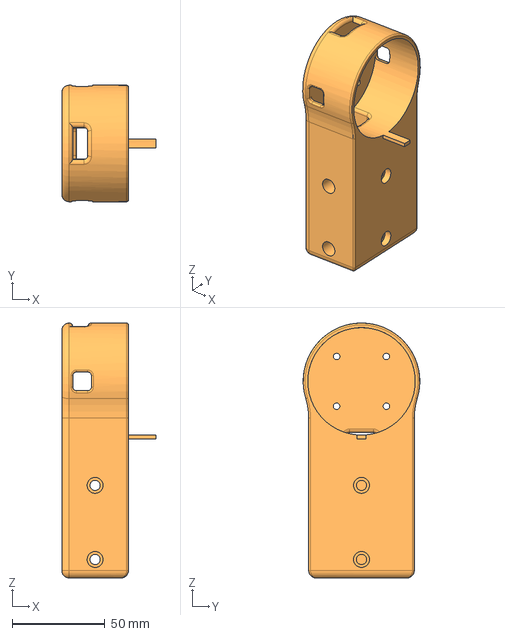
[picture p69: CAD file, 2026-07-16]
ume/robot/ume/ume_step/ume_v6_bimanual - v6_20_J2.step
51.0 x 63.0 x 137.7 mm
