inclusionAI/Universal-Manipulation-Exoskeleton/ume/robot/openarm1/models/meshes/visual/arm/link0_0.obj

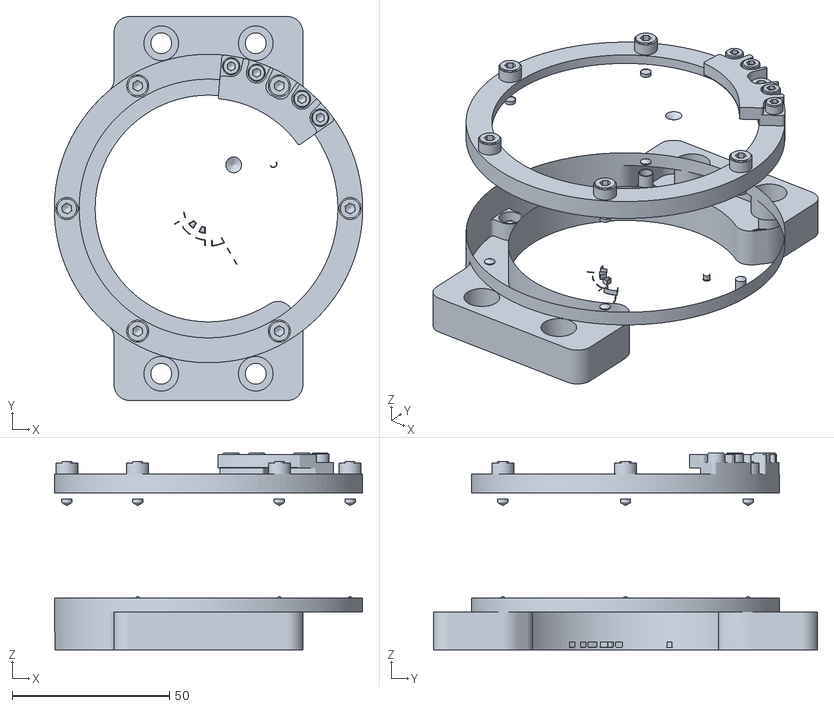
[picture p70: CAD file, 2026-07-16]
ume/robot/openarm1/models/meshes/visual/arm/link0_0.obj
98.0 x 122.0 x 62.5
