inclusionAI/Universal-Manipulation-Exoskeleton/ume/robot/ume/ume_step/ume_v6_bimanual - v6_J2_20.step

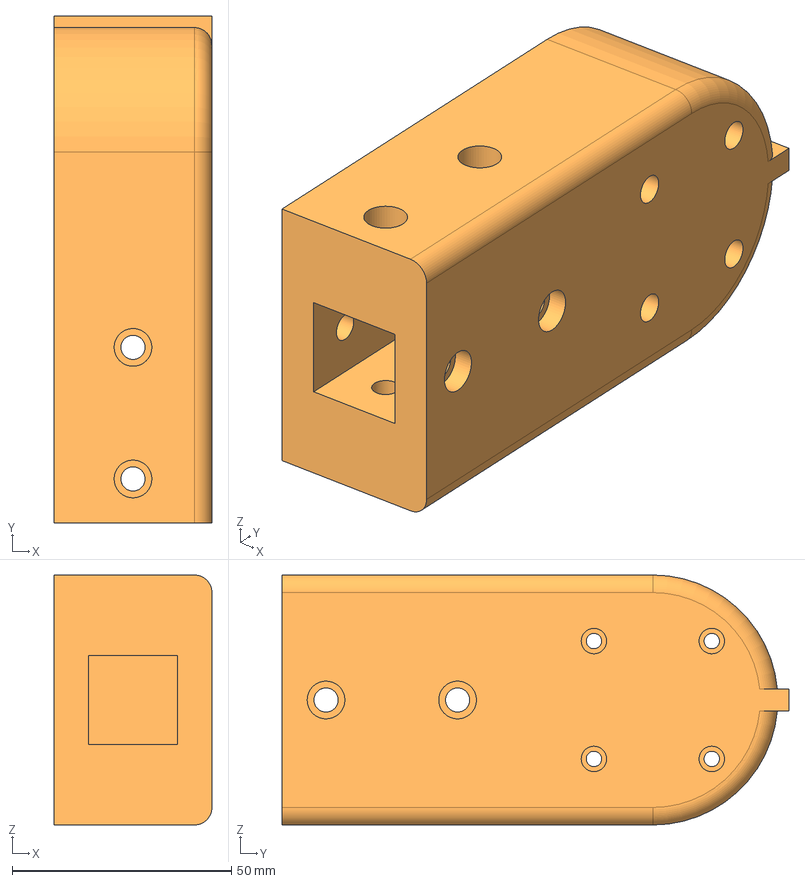
[picture p71: CAD file, 2026-07-16]
ume/robot/ume/ume_step/ume_v6_bimanual - v6_J2_20.step
36.0 x 115.5 x 57.0 mm
