inclusionAI/Universal-Manipulation-Exoskeleton/ume/robot/ume/ume_step/ume_v6_bimanual - v6_wrist_J5_J6.step

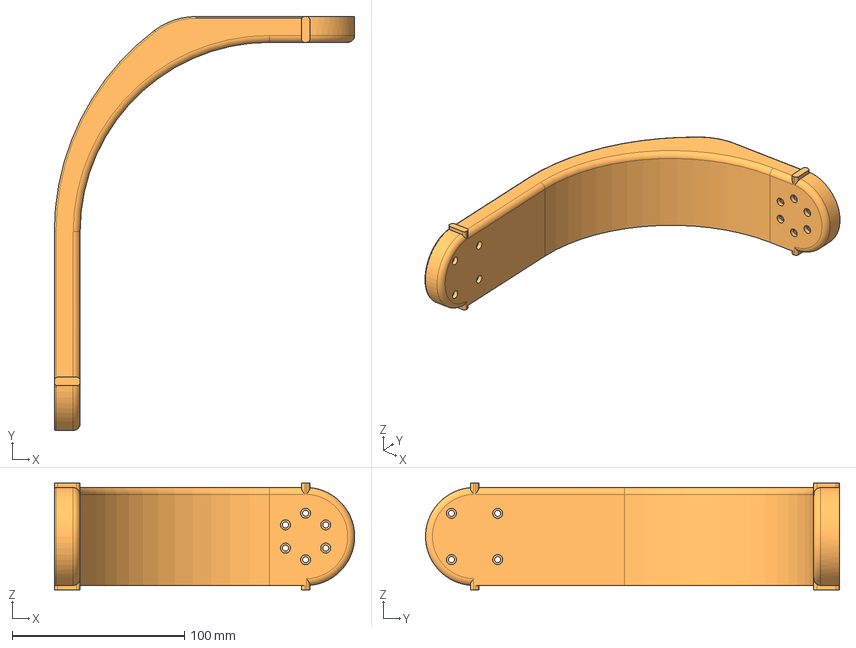
[picture p72: CAD file, 2026-07-16]
ume/robot/ume/ume_step/ume_v6_bimanual - v6_wrist_J5_J6.step
174.5 x 240.5 x 62.0 mm
