inclusionAI/Universal-Manipulation-Exoskeleton/ume/robot/ume/v6_imu/models/assets/v6_4040_belt.stl

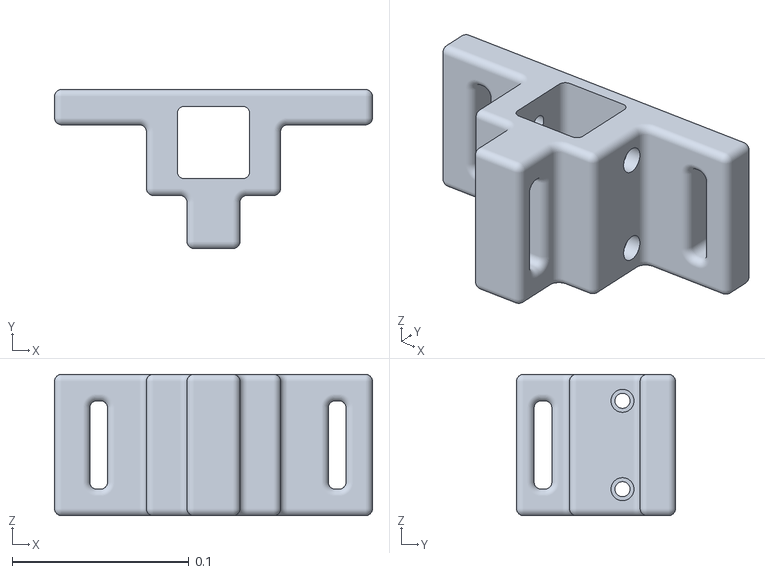
[picture p73: CAD file, 2026-07-16]
ume/robot/ume/v6_imu/models/assets/v6_4040_belt.stl
0.18 x 0.09 x 0.08
