inclusionAI/Universal-Manipulation-Exoskeleton/ume/robot/ume/ume_step/ume_v6_bimanual - v5_wrist_J7_leader_gripper_R.step

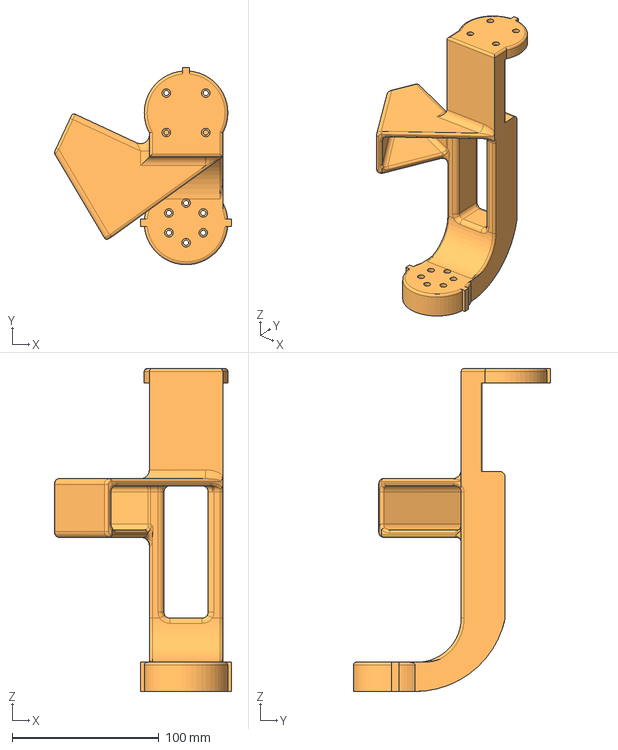
[picture p74: CAD file, 2026-07-16]
ume/robot/ume/ume_step/ume_v6_bimanual - v5_wrist_J7_leader_gripper_R.step
120.7 x 134.5 x 220.0 mm
