inclusionAI/Universal-Manipulation-Exoskeleton/ume/robot/ume/v6_imu/models/assets/4040_cap.stl

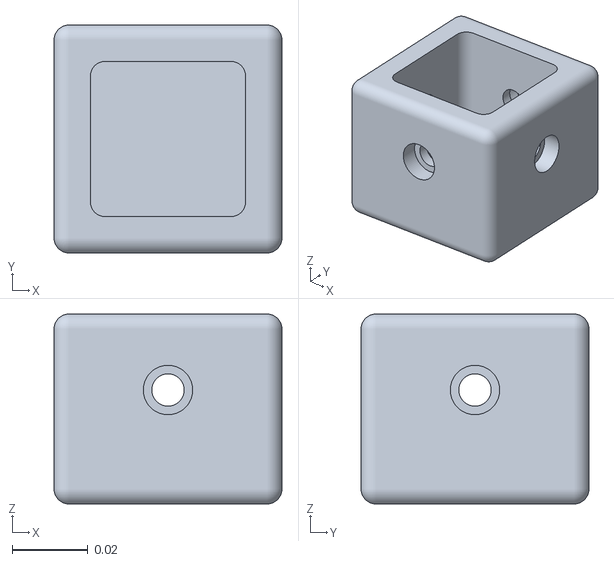
[picture p75: CAD file, 2026-07-16]
ume/robot/ume/v6_imu/models/assets/4040_cap.stl
0.06 x 0.06 x 0.05
