inclusionAI/Universal-Manipulation-Exoskeleton/ume/robot/ume/ume_step/ume_v6_bimanual - DM-J4340-2EC.step

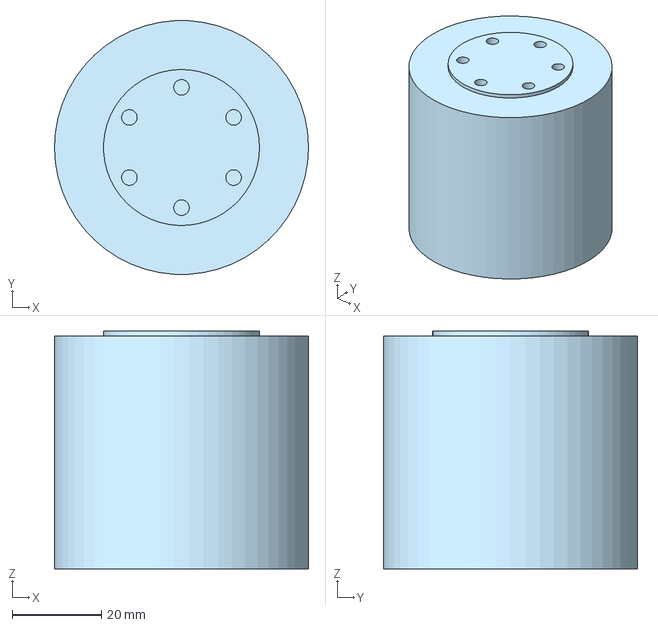
[picture p76: CAD file, 2026-07-16]
ume/robot/ume/ume_step/ume_v6_bimanual - DM-J4340-2EC.step
57.0 x 56.9 x 53.3 mm
