inclusionAI/Universal-Manipulation-Exoskeleton/ume/robot/ume/ume_step/ume_v6_bimanual - DM-J4310-2EC.step

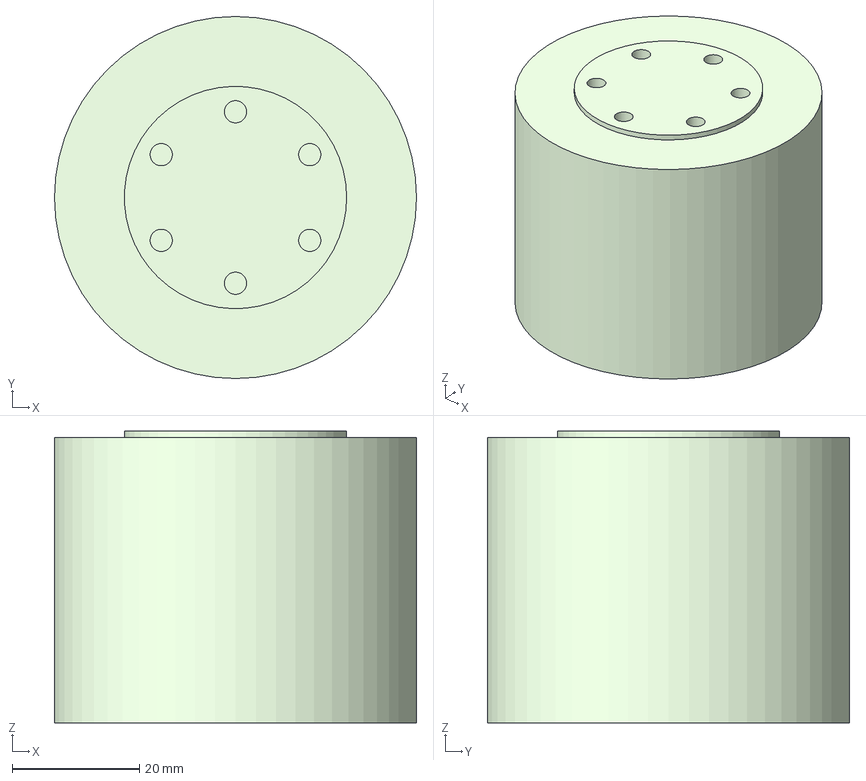
[picture p77: CAD file, 2026-07-16]
ume/robot/ume/ume_step/ume_v6_bimanual - DM-J4310-2EC.step
57.0 x 57.0 x 45.9 mm
