inclusionAI/Universal-Manipulation-Exoskeleton/ume/robot/ume/ume_step/ume_v6_bimanual - v6_20_J3.step

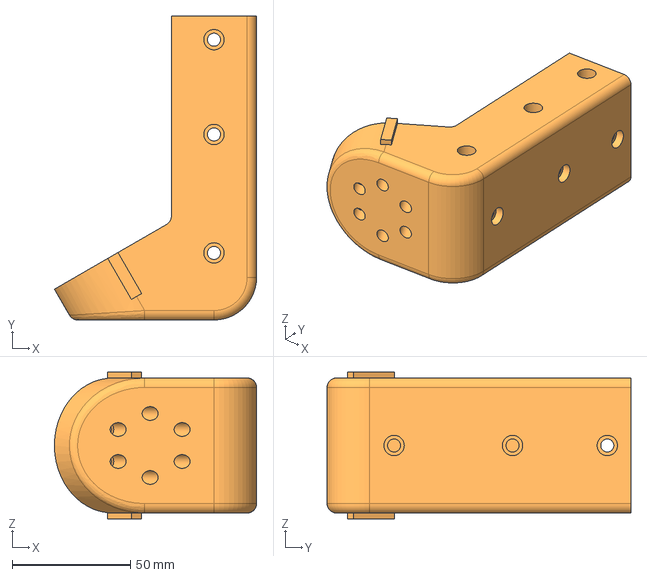
[picture p78: CAD file, 2026-07-16]
ume/robot/ume/ume_step/ume_v6_bimanual - v6_20_J3.step
85.4 x 128.3 x 62.0 mm
