inclusionAI/Universal-Manipulation-Exoskeleton/ume/robot/ume/ume_step/ume_v6_bimanual - v5_wrist_J6_J7.step

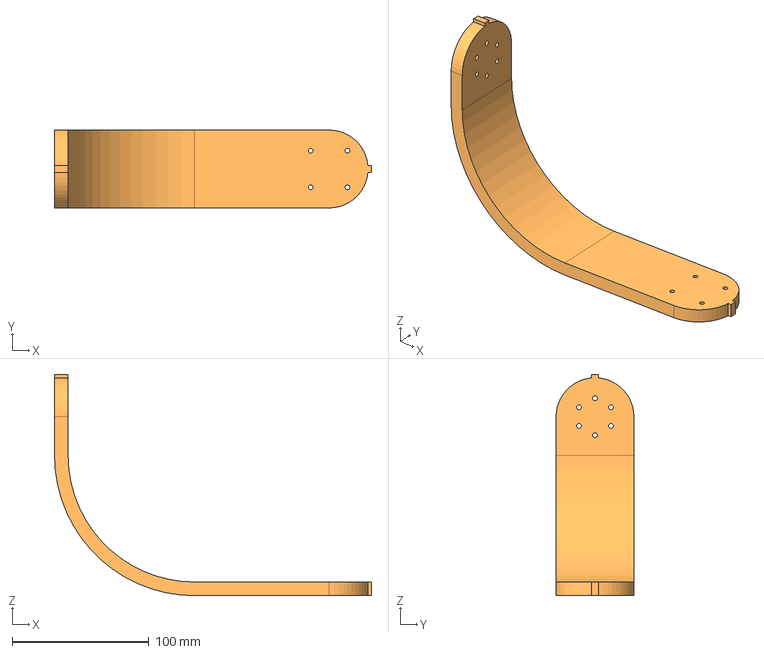
[picture p79: CAD file, 2026-07-16]
ume/robot/ume/ume_step/ume_v6_bimanual - v5_wrist_J6_J7.step
232.0 x 57.0 x 162.0 mm
