inclusionAI/Universal-Manipulation-Exoskeleton/ume/robot/ume/ume_step/ume_v6_bimanual - v6_J4_J5_L.step

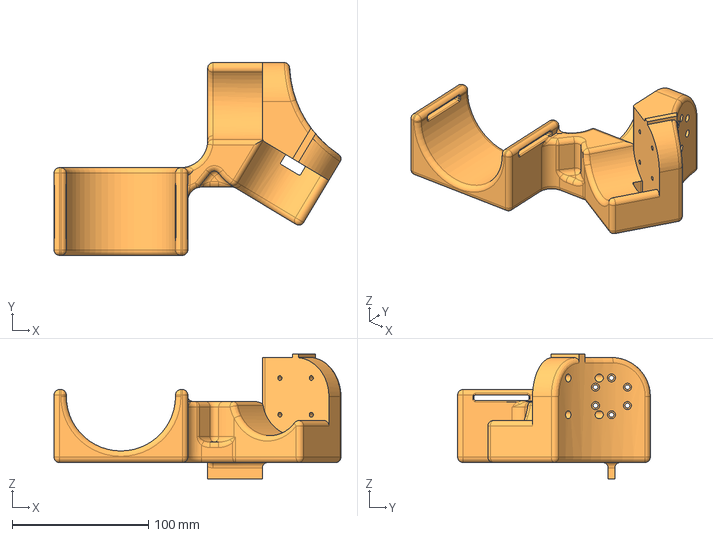
[picture p80: CAD file, 2026-07-16]
ume/robot/ume/ume_step/ume_v6_bimanual - v6_J4_J5_L.step
210.4 x 141.3 x 91.5 mm
