inclusionAI/Universal-Manipulation-Exoskeleton/ume/robot/ume/ume_step/ume_v6_bimanual - v5_4040_J1.step

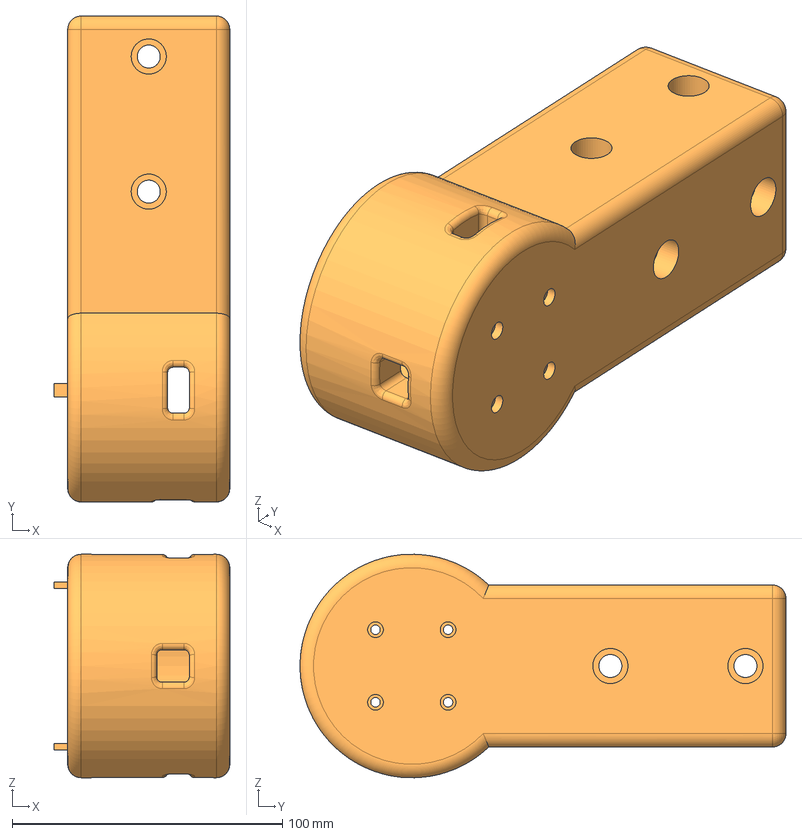
[picture p81: CAD file, 2026-07-16]
ume/robot/ume/ume_step/ume_v6_bimanual - v5_4040_J1.step
65.0 x 179.9 x 82.7 mm
