inclusionAI/Universal-Manipulation-Exoskeleton/ume/robot/ume/ume_step/ume_v6_bimanual - 4040x30cm.step

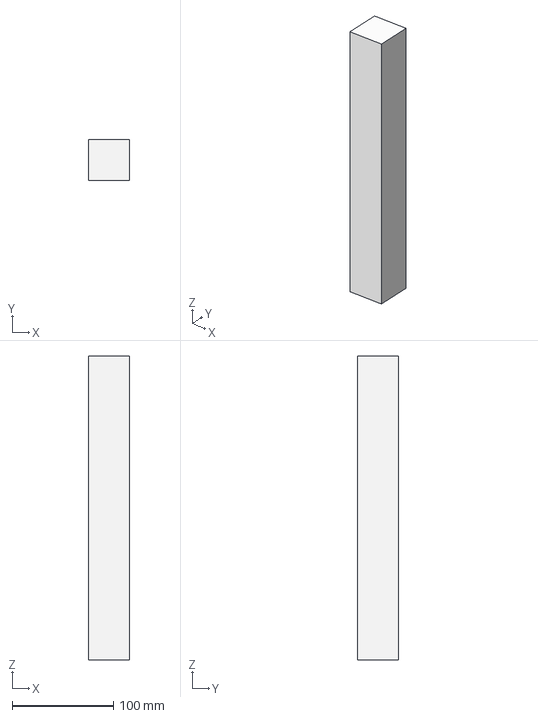
[picture p82: CAD file, 2026-07-16]
ume/robot/ume/ume_step/ume_v6_bimanual - 4040x30cm.step
40.0 x 40.0 x 300.0 mm
