inclusionAI/Universal-Manipulation-Exoskeleton/ume/robot/ume/ume_step/ume_v6_bimanual - v6_xt30_2+2_50cm.step

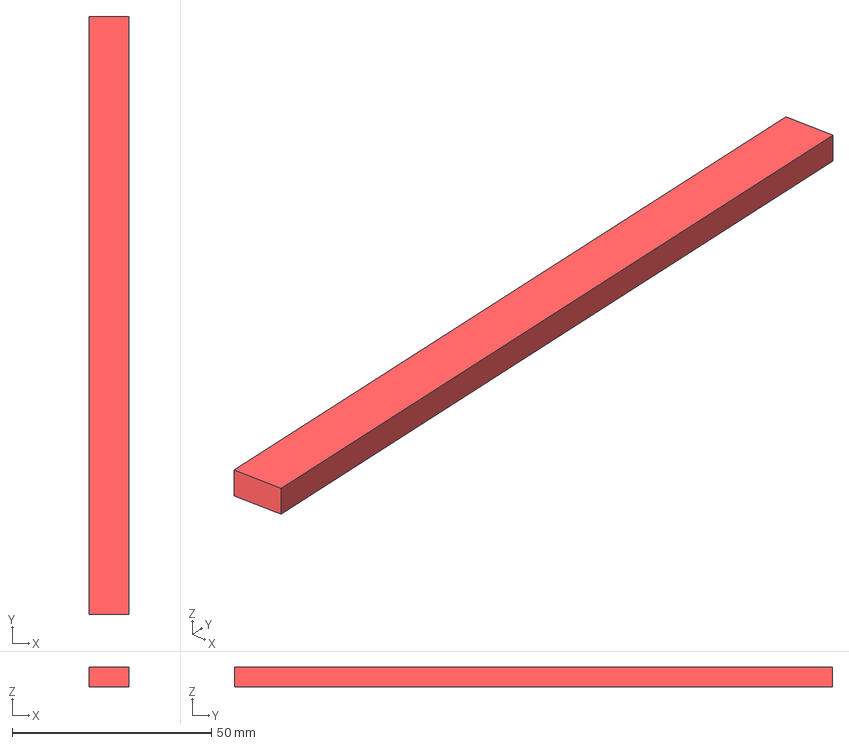
[picture p83: CAD file, 2026-07-16]
ume/robot/ume/ume_step/ume_v6_bimanual - v6_xt30_2+2_50cm.step
10.0 x 150.0 x 5.00 mm
